state-of-the-art/binocular/design/prototype_1/kicad/prototype_testboard-1/03_Connector.kicad_sch

## KiCad design design/prototype_1/kicad/prototype_testboard-1/03_Connector.kicad_sch (2022-01-14)

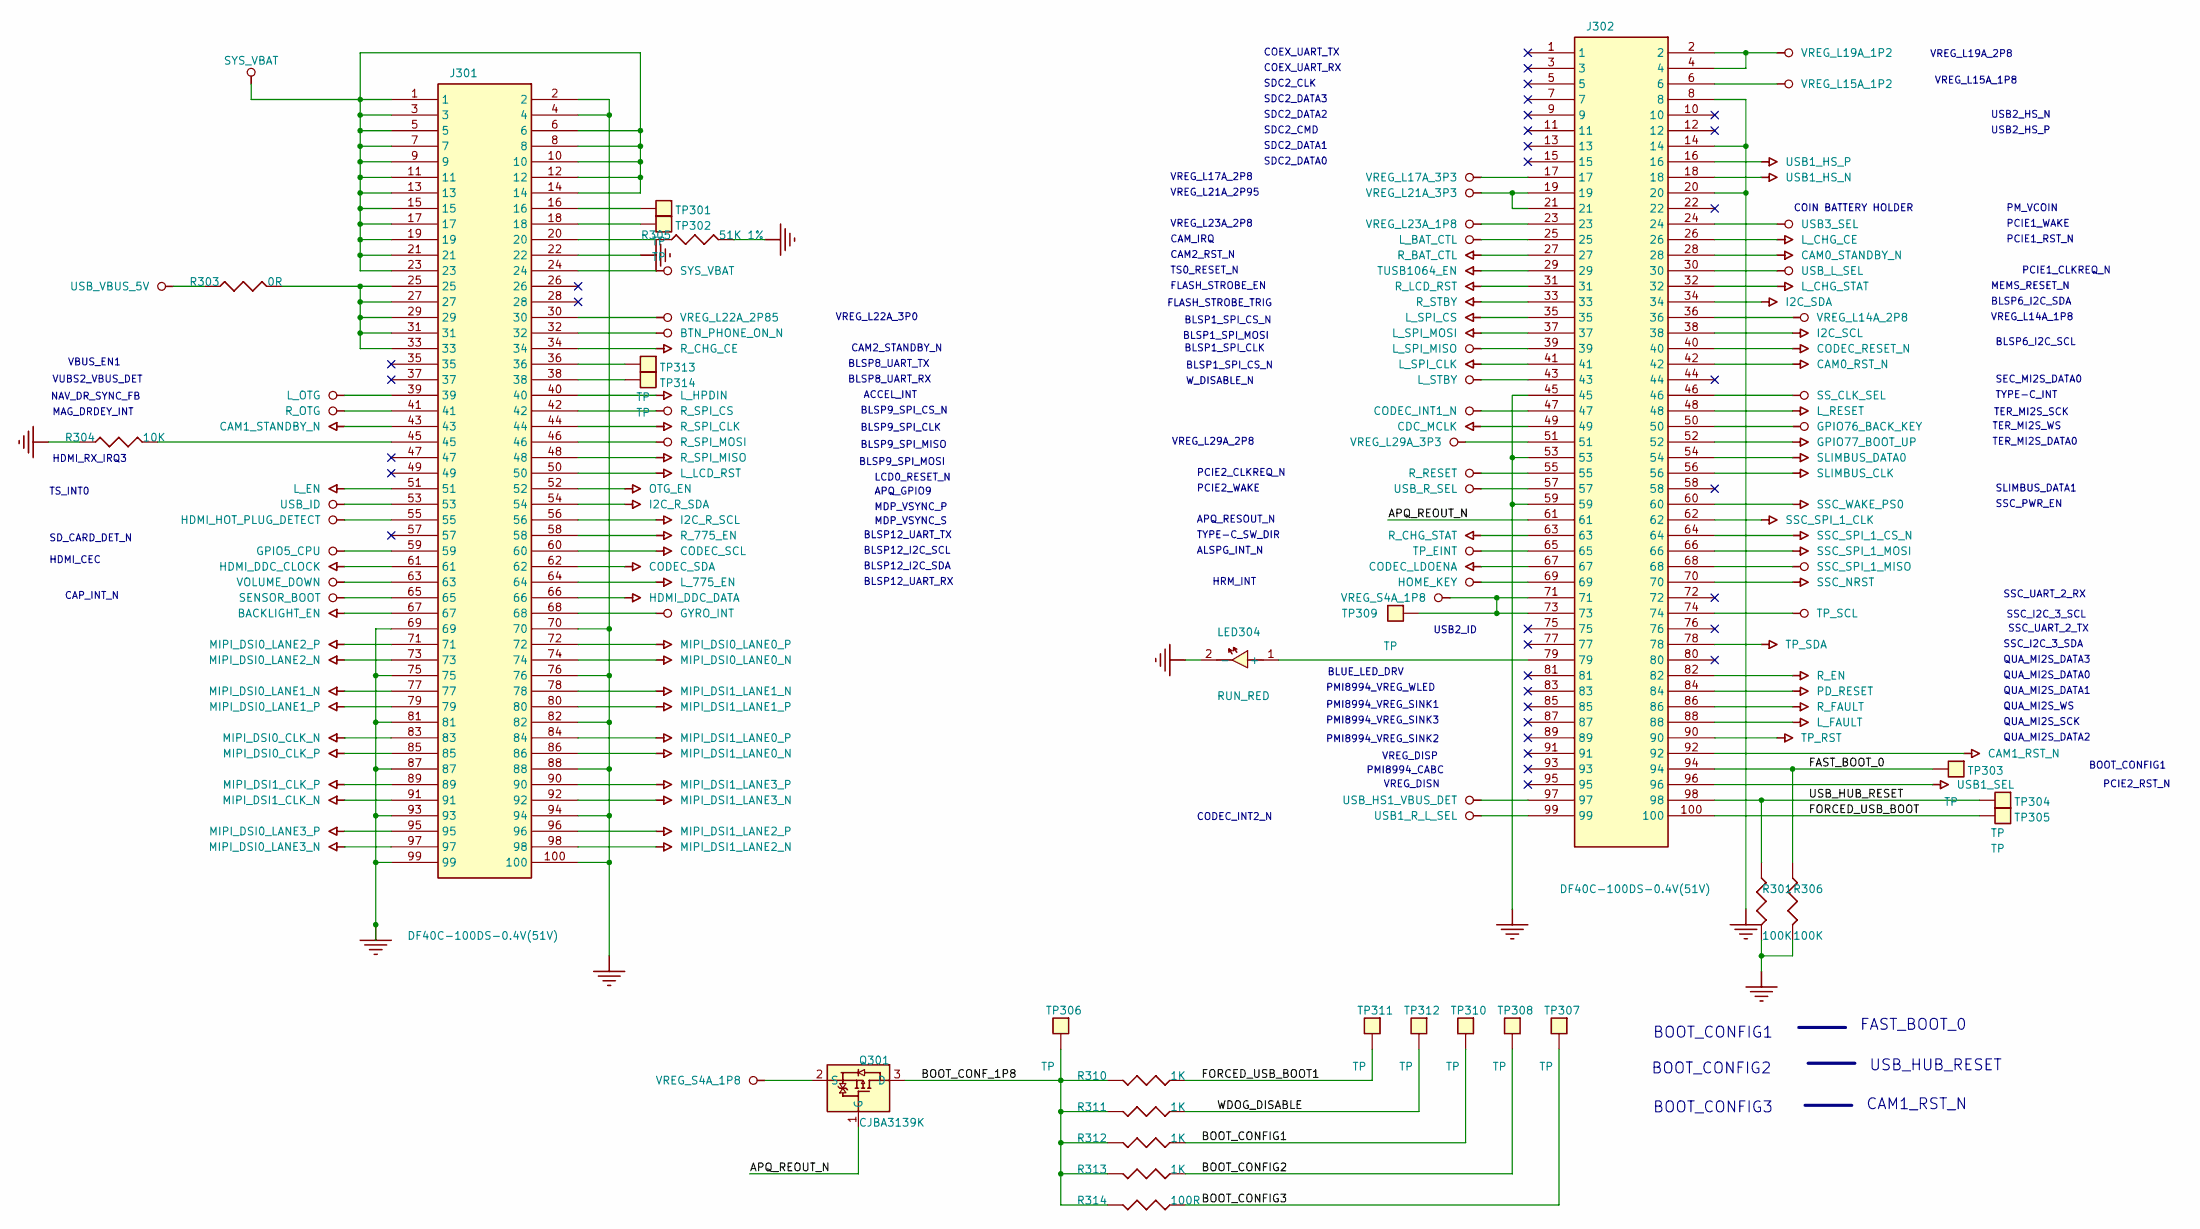
[picture p25: schematic 03_Connector.kicad_sch]

Parts:
J301, J302: DF40C-100DS-0.4V(51V); DF40C-100DS
LED304: RUN_RED; LED_0603
Q301: CJBA3139K; DFN1006-3L
R301, R306: 100K; R0201
R303: 0R; R0805
R304: 10K; R0201
R305: 51K 1%; R0201
R310, R311, R312, R313: 1K; R0201
R314: 100R; R0201
TP301, TP302, TP303, TP304, TP305, TP306, TP307, TP308, TP309, TP310, TP311, TP312, TP313, TP314: TP; TP-D1r0

Connections:
APQ_REOUT_N: J302.61, Q301.1 (G)
BOOT_CONFIG1: R312.1, TP310.1
BOOT_CONFIG2: R313.1, TP308.1
BOOT_CONFIG3: R314.1, TP307.1
BOOT_CONF_1P8: Q301.3 (D), R310.2, R311.2, R312.2, R313.2, R314.2, TP306.1
FAST_BOOT_0: J302.94, R306.1, TP303.1
FORCED_USB_BOOT: J302.100, TP305.1
FORCED_USB_BOOT1: R310.1, TP311.1
unnamed: J301.1, J301.3, J301.5, J301.6, J301.7, J301.8, J301.9, J301.10, J301.11, J301.12, J301.13, J301.14, J301.15, J301.17, J301.19, J301.21, J301.23
unnamed: J301.16, TP301.1
unnamed: J301.18, TP302.1
unnamed: J301.20, R305.1
unnamed: J301.25, J301.27, J301.29, J301.31, J301.33, R303.2
unnamed: J301.36, TP313.1
unnamed: J301.38, TP314.1
unnamed: J301.45, R304.2
unnamed: J301.69, J301.75, J301.81, J301.87, J301.93, J301.99
unnamed: J301.2, J301.4, J301.70, J301.76, J301.82, J301.88, J301.94, J301.100
unnamed: J302.2, J302.4
unnamed: J302.8, J302.14, J302.20
unnamed: J302.19, J302.21
unnamed: J302.45, J302.53, J302.59
unnamed: J302.71, J302.73, TP309.1
unnamed: J302.79, LED304.1 (+)
unnamed: R301.2, R306.2
USB_HUB_RESET: J302.98, R301.1, TP304.1
WDOG_DISABLE: R311.1, TP312.1

Notes on the sheet:
APQ_GPIO9
HDMI_CEC
BLSP12_I2C_SCL
VUBS2_VBUS_DET
BLSP1_SPI_CLK
BLSP9_SPI_CLK
QUA_MI2S_DATA3
SDC2_CLK
BLSP1_SPI_CS_N
VREG_DISP
MDP_VSYNC_P
QUA_MI2S_DATA1
BLUE_LED_DRV
USB2_HS_N
COEX_UART_RX
CAM2_STANDBY_N
PCIE2_RST_N
TS_INT0
SSC_UART_2_TX
MAG_DRDEY_INT
BOOT_CONFIG1
CAM2_RST_N
PMI8994_CABC
FLASH_STROBE_TRIG
BLSP12_UART_RX
VREG_L29A_2P8
PMI8994_VREG_SINK1
TS0_RESET_N
ALSPG_INT_N
COEX_UART_TX
MEMS_RESET_N
QUA_MI2S_WS
CODEC_INT2_N
CAM1_RST_N
VBUS_EN1
SD_CARD_DET_N
BLSP8_UART_RX
QUA_MI2S_SCK
PCIE1_WAKE
VREG_DISN
PCIE1_RST_N
USB2_ID
PM_VCOIN
SSC_UART_2_RX
SSC_I2C_3_SCL
USB2_HS_P
SEC_MI2S_DATA0
COIN BATTERY HOLDER
VREG_L23A_2P8
VREG_L17A_2P8
QUA_MI2S_DATA0
MDP_VSYNC_S
BLSP1_SPI_MOSI
PCIE1_CLKREQ_N
SDC2_DATA3
TYPE-C_SW_DIR
VREG_L21A_2P95
PMI8994_VREG_SINK3
VREG_L19A_2P8
SDC2_DATA0
BOOT_CONFIG2
PMI8994_VREG_WLED
HRM_INT
BLSP9_SPI_MISO
TER_MI2S_WS
BLSP6_I2C_SDA
BOOT_CONFIG3
BLSP8_UART_TX
LCD0_RESET_N
FLASH_STROBE_EN
SSC_I2C_3_SDA
PCIE2_CLKREQ_N
TER_MI2S_DATA0
BLSP12_UART_TX
PCIE2_WAKE
W_DISABLE_N
VREG_L15A_1P8
SDC2_DATA1
ACCEL_INT
NAV_DR_SYNC_FB
CAP_INT_N
BLSP6_I2C_SCL
BLSP12_I2C_SDA
FAST_BOOT_0
PMI8994_VREG_SINK2
SDC2_DATA2
HDMI_RX_IRQ3
TYPE-C_INT
TER_MI2S_SCK
CAM_IRQ
SDC2_CMD
APQ_RESOUT_N
VREG_L22A_3P0
SSC_PWR_EN
VREG_L14A_1P8
BLSP9_SPI_MOSI
SLIMBUS_DATA1
BLSP9_SPI_CS_N
QUA_MI2S_DATA2
USB_HUB_RESET
