state-of-the-art/binocular/design/prototype_1/kicad/prototype_testboard-1/04_TUSB564.kicad_sch

## KiCad design design/prototype_1/kicad/prototype_testboard-1/04_TUSB564.kicad_sch (2022-01-14)

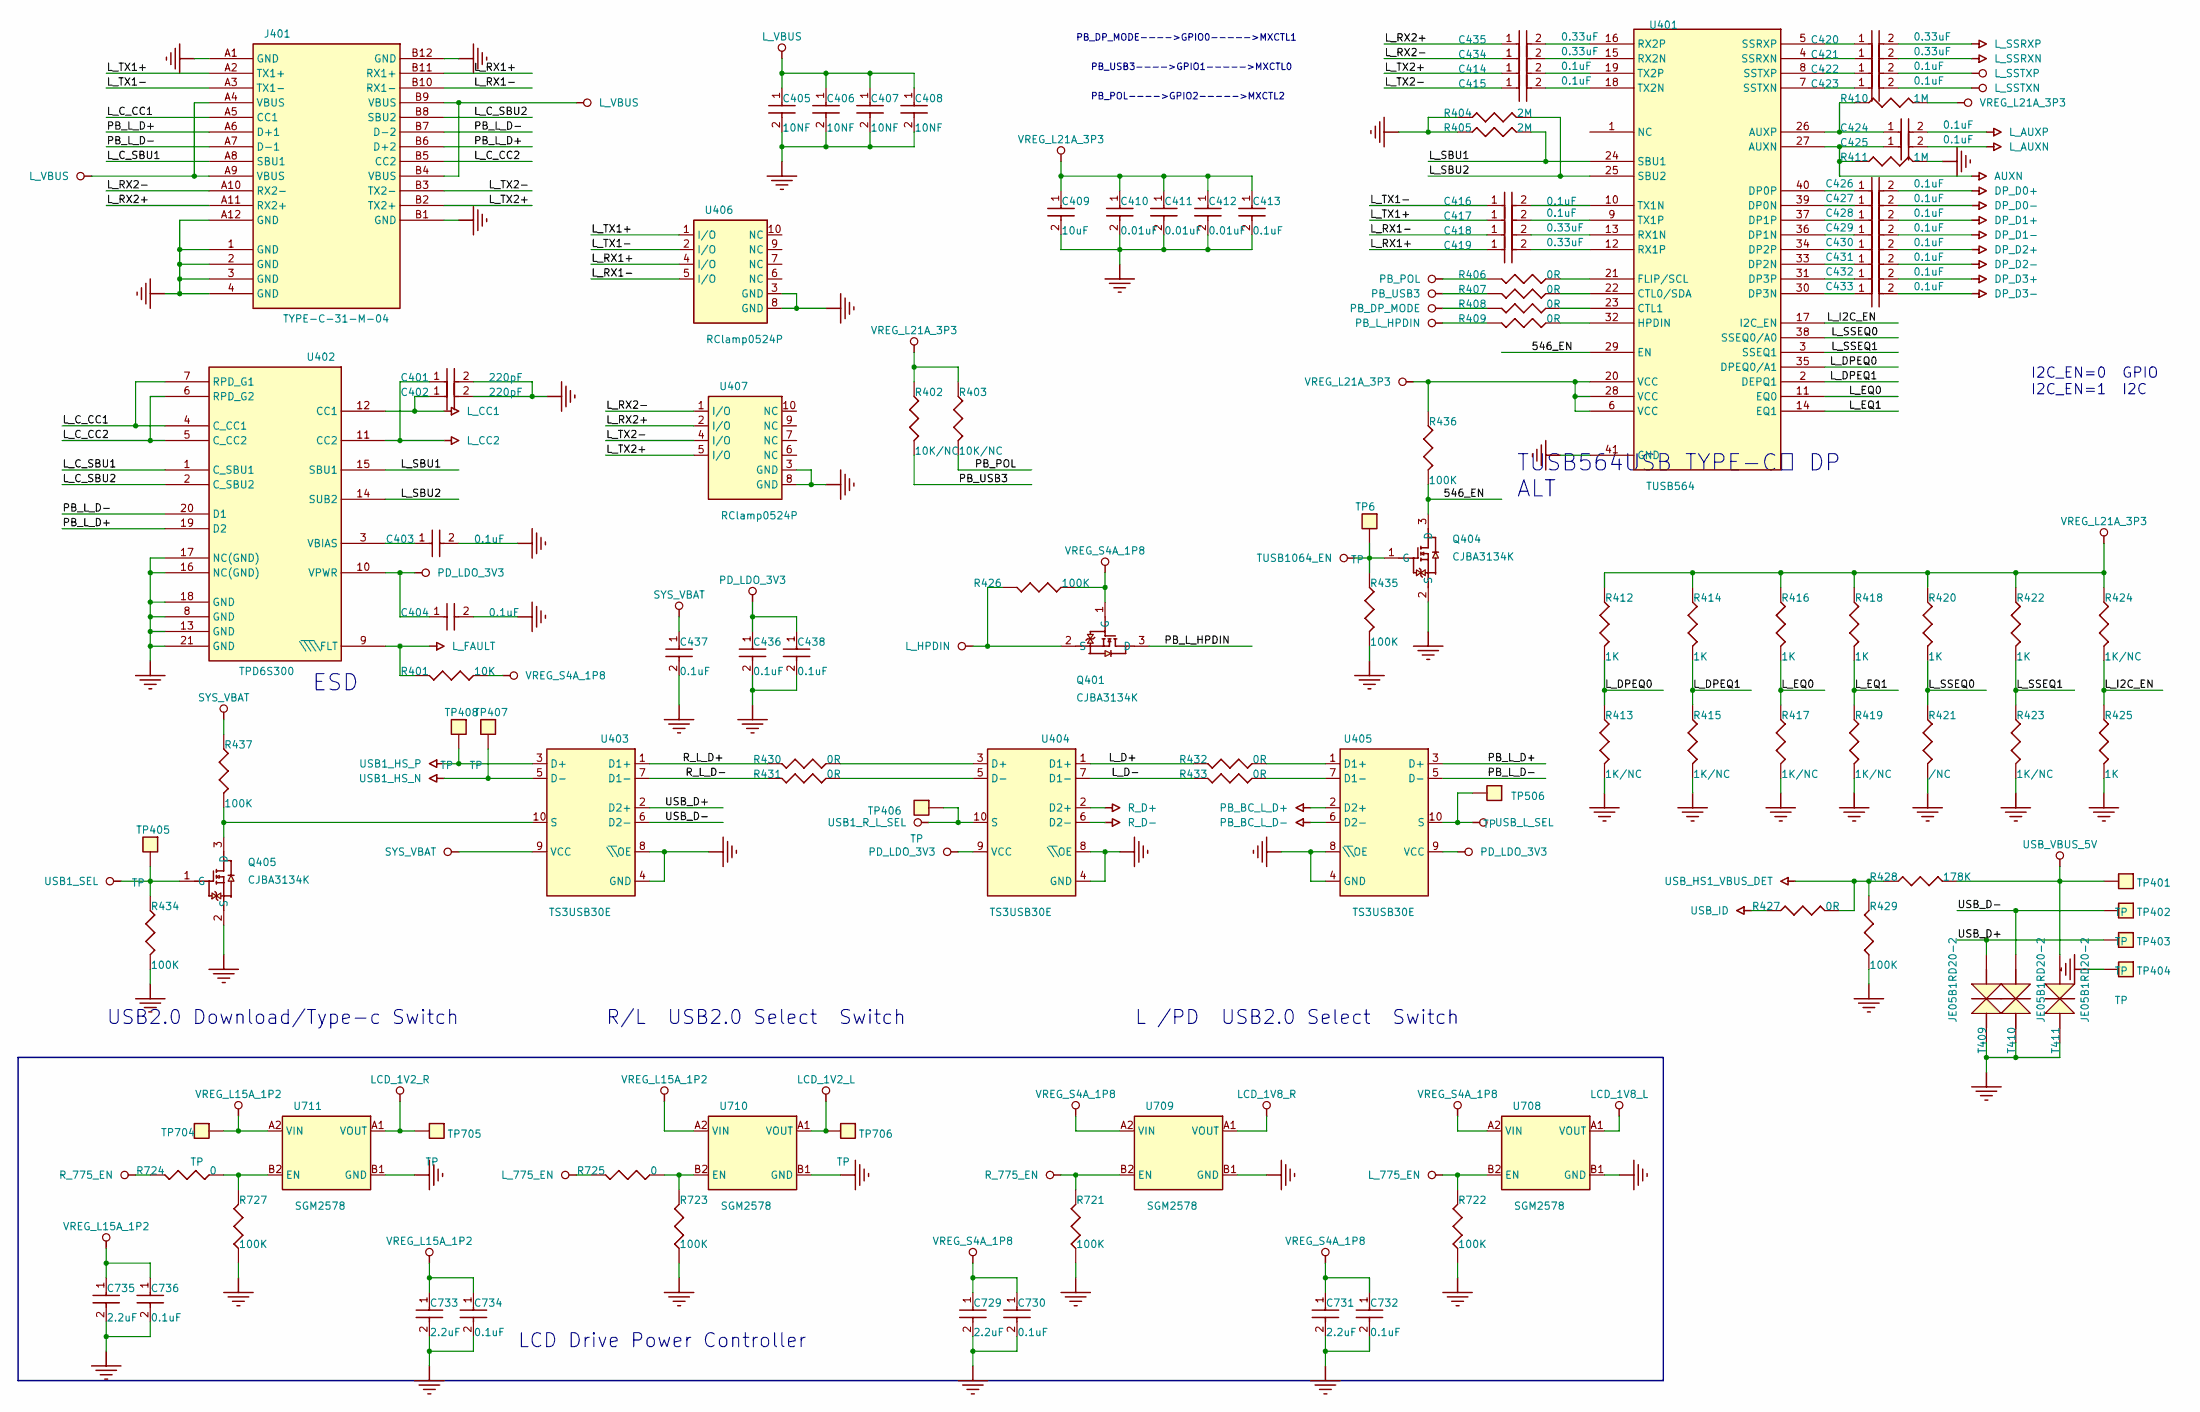
[picture p26: schematic 04_TUSB564.kicad_sch]

Parts:
C401, C402: 220pF; C0201
C403, C404, C413, C414, C415, C416, C417, C422, C423, C424, C425, C426, C427, C428, C429, C430, C431, C432, C433, C436, C437, C438, C730, C732, C734, C736: 0.1uF; C0201
C405, C406, C407, C408: 10NF; C0201
C409: 10uF; C0201
C410, C411, C412: 0.01uF; C0201
C418, C419, C420, C421, C434, C435: 0.33uF; C0201
C729, C731, C733, C735: 2.2uF; C0201
J401: TYPE-C-31-M-04
Q401, Q404, Q405: CJBA3134K; DFN1006-3L
R401: 10K; R0201
R402, R403: 10K/NC; R0201
R404, R405: 2M; R0201
R406, R407, R408, R409, R427, R430, R431, R432, R433: 0R; R0201
R410, R411: 1M; R0201
R412, R414, R416, R418, R420, R422, R425: 1K; R0201
R413, R415, R417, R419, R423, R424: 1K/NC; R0201
R421: /NC; R0201
R426, R429, R434, R435, R436, R437, R721, R722, R723, R727: 100K; R0201
R428: 178K; R0201
R724, R725: 0; R0201
T409, T410, T411: JE05B1RD20-2; DFN1006-2; MANUFACTURER PART NUMBER RB551V-30TE-17
TP6, TP401, TP402, TP403, TP404, TP405, TP406, TP407, TP408, TP506, TP704, TP705, TP706: TP; TP-D1r0
U401: TUSB564; TUSB564_WQFN40
U402: TPD6S300; TPD6S300_WQFN
U403, U404, U405: TS3USB30E; TS3USB30E_UQFN
U406, U407: RClamp0524P
U708, U709, U710, U711: SGM2578; WLCSP-0r90r9-4B

Connections:
546_EN: Q404.3 (D), R436.2, U401.29 (EN)
L_C_CC1: J401.A5 (CC1), U402.4 (C_CC1), U402.7 (RPD_G1)
L_C_CC2: J401.B5 (CC2), U402.5 (C_CC2), U402.6 (RPD_G2)
L_C_SBU1: J401.A8 (SBU1), U402.1 (C_SBU1)
L_C_SBU2: J401.B8 (SBU2), U402.2 (C_SBU2)
L_D+: R432.2, U404.1 (D1+)
L_D-: R433.2, U404.7 (D1-)
L_DPEQ0: R412.2, R413.1, U401.35 (DPEQ0/A1)
L_DPEQ1: R414.2, R415.1, U401.2 (DEPQ1)
L_EQ0: R416.2, R417.1, U401.11 (EQ0)
L_EQ1: R418.2, R419.1, U401.14 (EQ1)
L_I2C_EN: R424.2, R425.1, U401.17 (I2C_EN)
L_RX1+: C419.1, J401.B11 (RX1+), U406.4 (I/O)
L_RX1-: C418.1, J401.B10 (RX1-), U406.5 (I/O)
L_RX2+: C435.1, J401.A11 (RX2+), U407.2 (I/O)
L_RX2-: C434.1, J401.A10 (RX2-), U407.1 (I/O)
L_SBU1: R405.2, U401.24 (SBU1), U402.15 (SBU1)
L_SBU2: R404.2, U401.25 (SBU2), U402.14 (SUB2)
L_SSEQ0: R420.2, R421.1, U401.38 (SSEQ0/A0)
L_SSEQ1: R422.2, R423.1, U401.3 (SSEQ1)
L_TX1+: C417.1, J401.A2 (TX1+), U406.1 (I/O)
L_TX1-: C416.1, J401.A3 (TX1-), U406.2 (I/O)
L_TX2+: C414.1, J401.B2 (TX2+), U407.5 (I/O)
L_TX2-: C415.1, J401.B3 (TX2-), U407.4 (I/O)
unnamed: C401.1, U402.11 (CC2)
unnamed: C401.2, C402.2
unnamed: C402.1, U402.12 (CC1)
unnamed: C403.1, U402.3 (VBIAS)
unnamed: C404.1, U402.10 (VPWR)
unnamed: C405.1, C406.1, C407.1, C408.1
unnamed: C405.2, C406.2, C407.2, C408.2
unnamed: C409.1, C410.1, C411.1, C412.1, C413.1
unnamed: C409.2, C410.2, C411.2, C412.2, C413.2
unnamed: C414.2, U401.19 (TX2P)
unnamed: C415.2, U401.18 (TX2N)
unnamed: C416.2, U401.10 (TX1N)
unnamed: C417.2, U401.9 (TX1P)
unnamed: C418.2, U401.13 (RX1N)
unnamed: C419.2, U401.12 (RX1P)
unnamed: C420.1, U401.5 (SSRXP)
unnamed: C421.1, U401.4 (SSRXN)
unnamed: C422.1, U401.8 (SSTXP)
unnamed: C423.1, U401.7 (SSTXN)
unnamed: C424.1, R410.1, U401.26 (AUXP)
unnamed: C425.1, R411.1, U401.27 (AUXN)
unnamed: C426.1, U401.40 (DP0P)
unnamed: C427.1, U401.39 (DP0N)
unnamed: C428.1, U401.37 (DP1P)
unnamed: C429.1, U401.36 (DP1N)
unnamed: C430.1, U401.34 (DP2P)
unnamed: C431.1, U401.33 (DP2N)
unnamed: C432.1, U401.31 (DP3P)
unnamed: C433.1, U401.30 (DP3N)
unnamed: C434.2, U401.15 (RX2N)
unnamed: C435.2, U401.16 (RX2P)
unnamed: C436.1, C438.1
unnamed: C436.2, C438.2
unnamed: C729.1, C730.1
unnamed: C729.2, C730.2
unnamed: C731.1, C732.1
unnamed: C731.2, C732.2
unnamed: C733.1, C734.1
unnamed: C733.2, C734.2
unnamed: C735.1, C736.1
unnamed: C735.2, C736.2
unnamed: J401.1 (GND), J401.2 (GND), J401.3 (GND), J401.4 (GND), J401.A12 (GND)
unnamed: J401.A4 (VBUS), J401.A9 (VBUS)
unnamed: J401.B4 (VBUS), J401.B9 (VBUS)
unnamed: Q401.1 (G), R426.1
unnamed: Q401.2 (S), R426.2
unnamed: Q404.1 (G), R435.1, TP6.1
unnamed: Q405.1 (G), R434.1, TP405.1
unnamed: Q405.3 (D), R437.2, U403.10 (S)
unnamed: R401.2, U402.9 (~\\\\FLT)
unnamed: R402.1, R403.1
unnamed: R404.1, R405.1
unnamed: R406.1, U401.21 (FLIP/SCL)
unnamed: R407.1, U401.22 (CTL0/SDA)
unnamed: R408.1, U401.23 (CTL1)
unnamed: R409.1, U401.32 (HPDIN)
unnamed: R412.1, R414.1, R416.1, R418.1, R420.1, R422.1, R424.1
unnamed: R427.2, R428.1, R429.2
unnamed: R428.2, T411.2 (-), TP401.1
unnamed: R430.1, U404.3 (D+)
unnamed: R431.1, U404.5 (D-)
unnamed: R432.1, U405.1 (D1+)
unnamed: R433.1, U405.7 (D1-)
unnamed: R436.1, U401.6 (VCC), U401.20 (VCC), U401.28 (VCC)
unnamed: R721.2, U709.B2 (EN)
unnamed: R722.2, U708.B2 (EN)
unnamed: R723.2, R725.1, U710.B2 (EN)
unnamed: R724.1, R727.2, U711.B2 (EN)
unnamed: T409.1 (+), T410.1 (+), T411.1 (+)
unnamed: TP406.1, U404.10 (S)
unnamed: TP407.1, U403.5 (D-)
unnamed: TP408.1, U403.3 (D+)
unnamed: TP506.1, U405.10 (S)
unnamed: TP704.1, U711.A2 (VIN)
unnamed: TP705.1, U711.A1 (VOUT)
unnamed: TP706.1, U710.A1 (VOUT)
unnamed: U402.8 (GND), U402.13 (GND), U402.16 (NC(GND)), U402.17 (NC(GND)), U402.18 (GND), U402.21 (GND)
unnamed: U403.4 (GND), U403.8 (~\\OE)
unnamed: U404.4 (GND), U404.8 (~\\OE)
unnamed: U405.4 (GND), U405.8 (~\\OE)
unnamed: U406.3 (GND), U406.8 (GND)
unnamed: U407.3 (GND), U407.8 (GND)
PB_L_D+: J401.A6 (D+1), J401.B6 (D+2), U402.19 (D2), U405.3 (D+)
PB_L_D-: J401.A7 (D-1), J401.B7 (D-2), U402.20 (D1), U405.5 (D-)
PB_L_HPDIN: Q401.3 (D)
PB_POL: R403.2
PB_USB3: R402.2
R_L_D+: R430.2, U403.1 (D1+)
R_L_D-: R431.2, U403.7 (D1-)
USB_D+: T409.2 (-), TP403.1, U403.2 (D2+)
USB_D-: T410.2 (-), TP402.1, U403.6 (D2-)

Notes on the sheet:
LCD Drive Power Controller
TUSB564USB TYPE-C™ DP ALT
R/L USB2.0 Select Switch
PB_DP_MODE---->GPIO0----->MXCTL1
L /PD USB2.0 Select Switch
PB_POL---->GPIO2----->MXCTL2
USB2.0 Download/Type-c Switch
ESD
I2C_EN=0 GPIO I2C_EN=1 I2C
PB_USB3---->GPIO1----->MXCTL0
