state-of-the-art/binocular/design/prototype_1/kicad/prototype_testboard-1/05_TUSB546-DSI.kicad_sch

## KiCad design design/prototype_1/kicad/prototype_testboard-1/05_TUSB546-DSI.kicad_sch (2022-01-14)

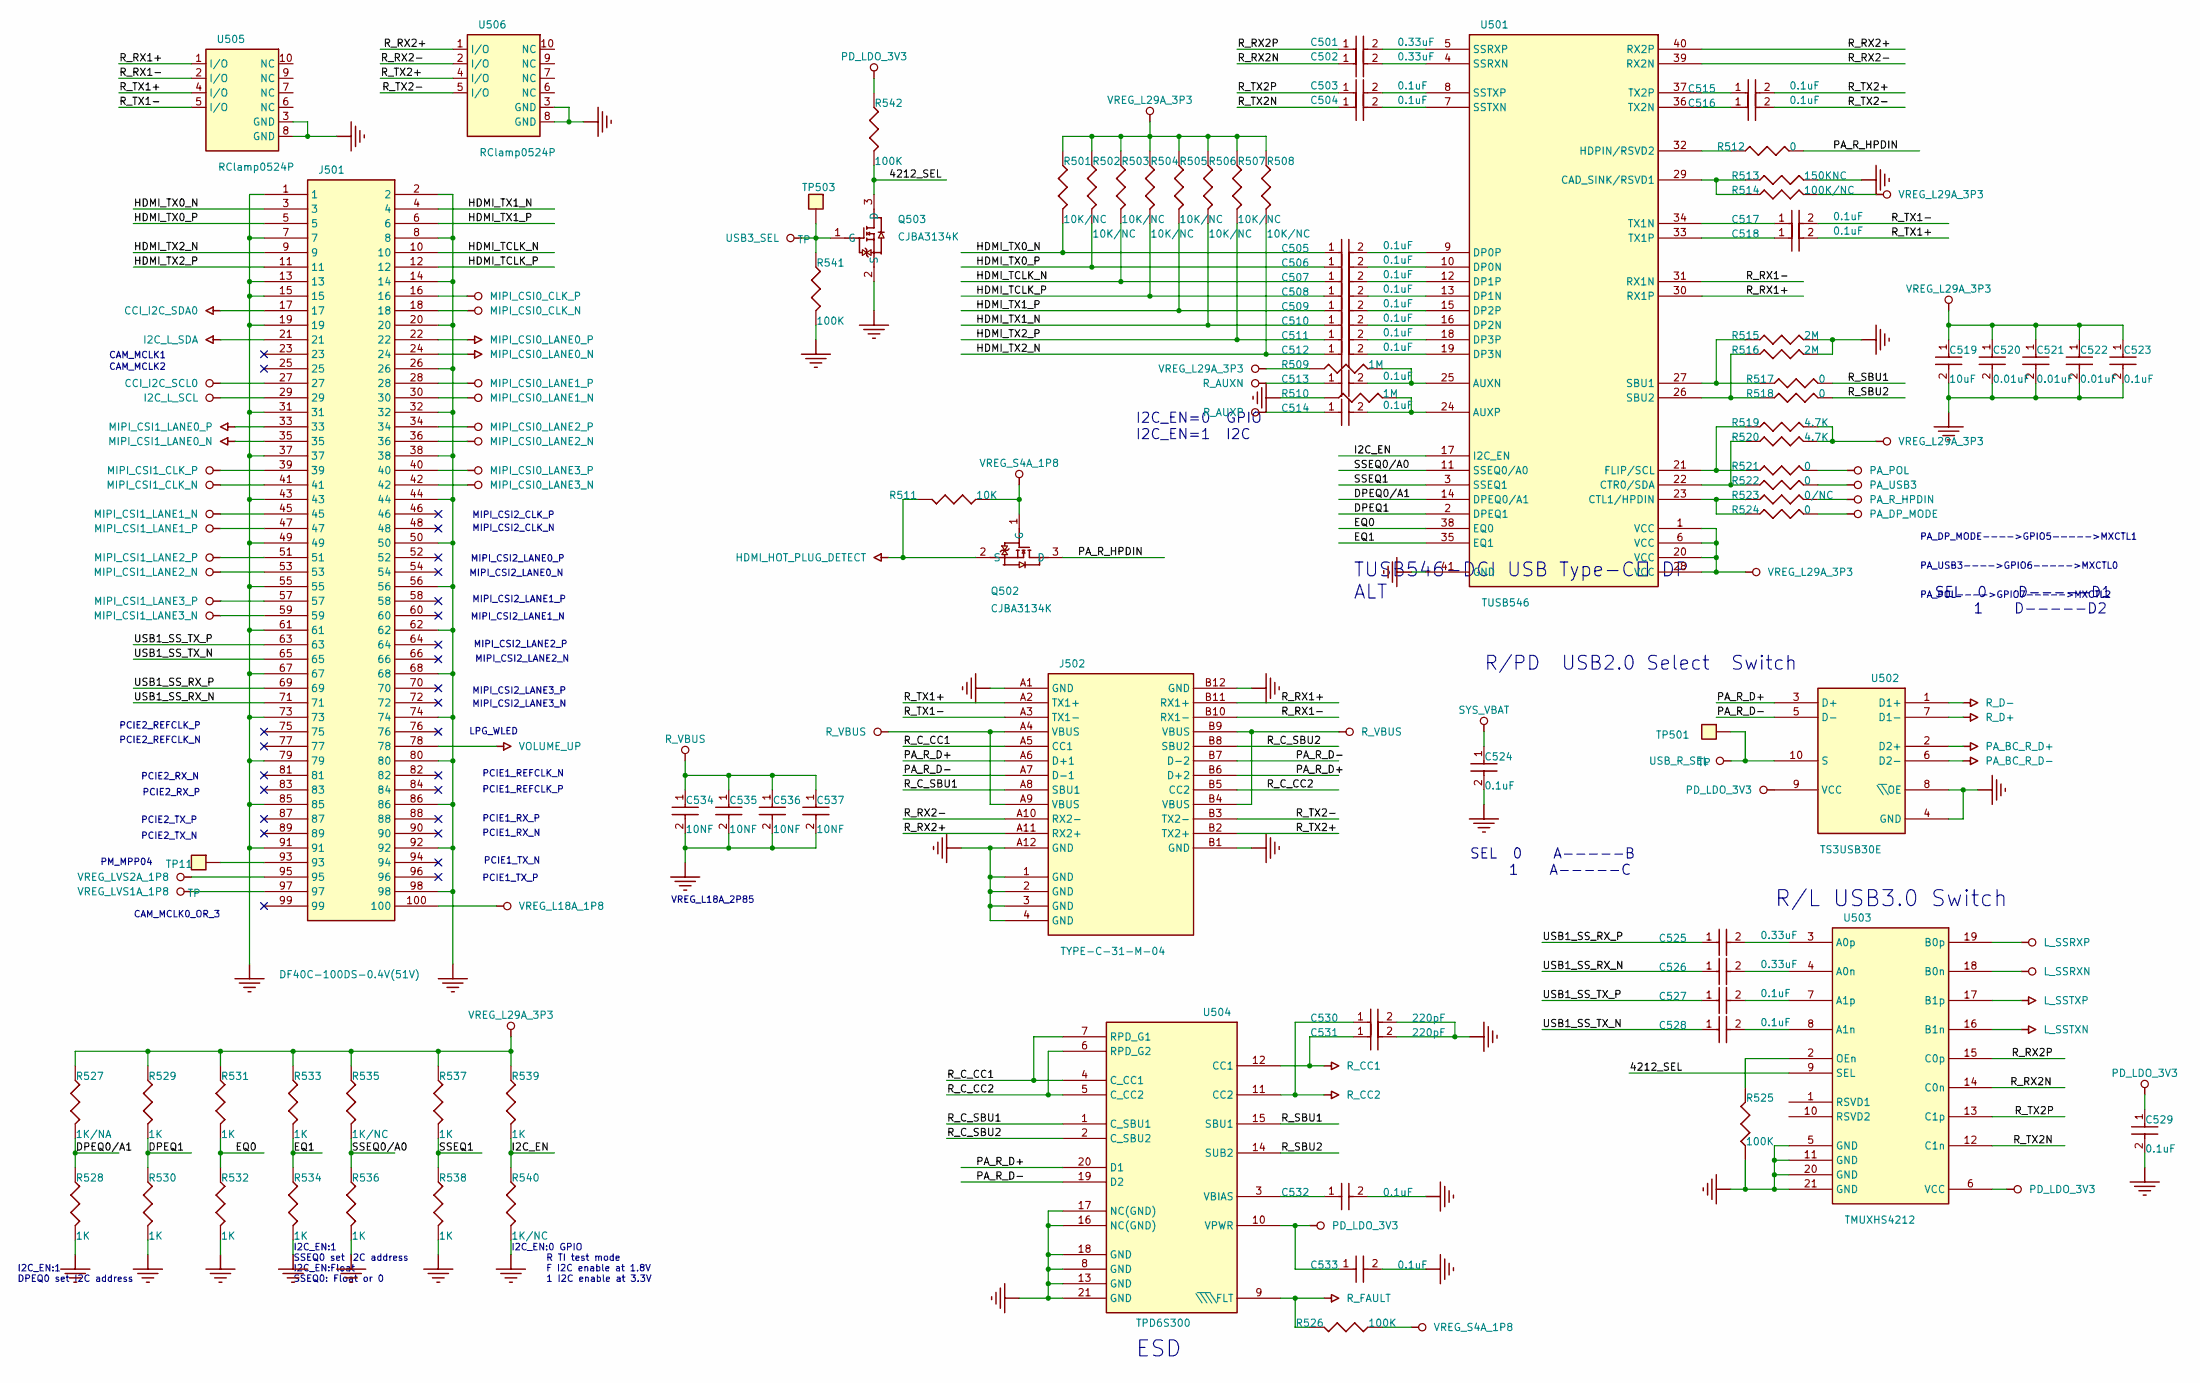
[picture p27: schematic 05_TUSB546-DSI.kicad_sch]

Parts:
C501, C502, C525, C526: 0.33uF; C0201
C503, C504, C505, C506, C507, C508, C509, C510, C511, C512, C513, C514, C515, C516, C517, C518, C523, C524, C527, C528, C529, C532, C533: 0.1uF; C0201
C519: 10uF; C0201
C520, C521, C522: 0.01uF; C0201
C530, C531: 220pF; C0201
C534, C535, C536, C537: 10NF; C0201
J501: DF40C-100DS-0.4V(51V); DF40C-100DS
J502: TYPE-C-31-M-04
Q502, Q503: CJBA3134K; DFN1006-3L
R501, R502, R503, R504, R505, R506, R507, R508: 10K/NC; R0201
R509, R510: 1M; R0201
R511: 10K; R0201
R512, R517, R518, R521, R522, R524: 0; R0201
R513: 150KNC; R0201
R514: 100K/NC; R0201
R515, R516: 2M; R0201
R519, R520: 4.7K; R0201
R523: 0/NC; R0201
R525, R526, R541, R542: 100K; R0201
R527: 1K/NA; R0201
R528, R529, R530, R531, R532, R533, R534, R536, R537, R538, R539: 1K; R0201
R535, R540: 1K/NC; R0201
TP11, TP501, TP503: TP; TP-D1r0
U501: TUSB546; TUSB564_WQFN40
U502: TS3USB30E; TS3USB30E_UQFN
U503: TMUXHS4212; TMUXHS4212_VQFN
U504: TPD6S300; TPD6S300_WQFN
U505, U506: RClamp0524P

Connections:
4212_SEL: Q503.3 (D), R542.2, U503.9 (SEL)
DPEQ0/A1: R527.2, R528.1, U501.14 (DPEQ0/A1)
DPEQ1: R529.2, R530.1, U501.2 (DPEQ1)
EQ0: R531.2, R532.1, U501.38 (EQ0)
EQ1: R533.2, R534.1, U501.35 (EQ1)
HDMI_TCLK_N: C507.1, J501.10, R503.2
HDMI_TCLK_P: C508.1, J501.12, R504.2
HDMI_TX0_N: C505.1, J501.3, R501.2
HDMI_TX0_P: C506.1, J501.5, R502.2
HDMI_TX1_N: C510.1, J501.4, R506.2
HDMI_TX1_P: C509.1, J501.6, R505.2
HDMI_TX2_N: C512.1, J501.9, R508.2
HDMI_TX2_P: C511.1, J501.11, R507.2
I2C_EN: R539.2, R540.1, U501.17 (I2C_EN)
unnamed: C501.2, U501.5 (SSRXP)
unnamed: C502.2, U501.4 (SSRXN)
unnamed: C503.2, U501.8 (SSTXP)
unnamed: C504.2, U501.7 (SSTXN)
unnamed: C505.2, U501.9 (DP0P)
unnamed: C506.2, U501.10 (DP0N)
unnamed: C507.2, U501.12 (DP1P)
unnamed: C508.2, U501.13 (DP1N)
unnamed: C509.2, U501.15 (DP2P)
unnamed: C510.2, U501.16 (DP2N)
unnamed: C511.2, U501.18 (DP3P)
unnamed: C512.2, U501.19 (DP3N)
unnamed: C513.2, R509.2, U501.25 (AUXN)
unnamed: C514.2, R510.2, U501.24 (AUXP)
unnamed: C515.1, U501.37 (TX2P)
unnamed: C516.1, U501.36 (TX2N)
unnamed: C517.1, U501.34 (TX1N)
unnamed: C518.1, U501.33 (TX1P)
unnamed: C519.1, C520.1, C521.1, C522.1, C523.1
unnamed: C519.2, C520.2, C521.2, C522.2, C523.2
unnamed: C525.2, U503.3 (A0p)
unnamed: C526.2, U503.4 (A0n)
unnamed: C527.2, U503.7 (A1p)
unnamed: C528.2, U503.8 (A1n)
unnamed: C530.1, U504.11 (CC2)
unnamed: C530.2, C531.2
unnamed: C531.1, U504.12 (CC1)
unnamed: C532.1, U504.3 (VBIAS)
unnamed: C533.1, U504.10 (VPWR)
unnamed: C534.1, C535.1, C536.1, C537.1
unnamed: C534.2, C535.2, C536.2, C537.2
unnamed: J501.1, J501.7, J501.13, J501.15, J501.19, J501.31, J501.37, J501.43, J501.49, J501.55, J501.61, J501.67, J501.73, J501.79, J501.85, J501.91
unnamed: J501.2, J501.8, J501.14, J501.20, J501.26, J501.32, J501.38, J501.44, J501.50, J501.56, J501.62, J501.68, J501.74, J501.80, J501.86, J501.92, J501.98
unnamed: J501.93, TP11.1
unnamed: J502.1 (GND), J502.2 (GND), J502.3 (GND), J502.4 (GND), J502.A12 (GND)
unnamed: J502.A4 (VBUS), J502.A9 (VBUS)
unnamed: J502.B4 (VBUS), J502.B9 (VBUS)
unnamed: Q502.1 (G), R511.1
unnamed: Q502.2 (S), R511.2
unnamed: Q503.1 (G), R541.1, TP503.1
unnamed: R501.1, R502.1, R503.1, R504.1, R505.1, R506.1, R507.1, R508.1
unnamed: R512.1, U501.32 (HDPIN/RSVD2)
unnamed: R513.1, R514.1, U501.29 (CAD_SINK/RSVD1)
unnamed: R515.1, R517.1, U501.27 (SBU1)
unnamed: R515.2, R516.2
unnamed: R516.1, R518.1, U501.26 (SBU2)
unnamed: R519.1, R521.1, U501.21 (FLIP/SCL)
unnamed: R519.2, R520.2
unnamed: R520.1, R522.1, U501.22 (CTR0/SDA)
unnamed: R523.1, R524.1, U501.23 (CTL1/HPDIN)
unnamed: R525.1, U503.5 (GND), U503.11 (GND), U503.20 (GND), U503.21 (GND)
unnamed: R525.2, U503.2 (OEn)
unnamed: R526.2, U504.9 (~\\\\FLT)
unnamed: R527.1, R529.1, R531.1, R533.1, R535.1, R537.1, R539.1
unnamed: TP501.1, U502.10 (S)
unnamed: U501.1 (VCC), U501.6 (VCC), U501.20 (VCC), U501.28 (VCC)
unnamed: U502.4 (GND), U502.8 (~\\OE)
unnamed: U504.8 (GND), U504.13 (GND), U504.16 (NC(GND)), U504.17 (NC(GND)), U504.18 (GND), U504.21 (GND)
unnamed: U505.3 (GND), U505.8 (GND)
unnamed: U506.3 (GND), U506.8 (GND)
PA_R_D+: J502.A6 (D+1), J502.B6 (D+2), U502.3 (D+), U504.20 (D1)
PA_R_D-: J502.A7 (D-1), J502.B7 (D-2), U502.5 (D-), U504.19 (D2)
PA_R_HPDIN: Q502.3 (D), R512.2
R_C_CC1: J502.A5 (CC1), U504.4 (C_CC1), U504.7 (RPD_G1)
R_C_CC2: J502.B5 (CC2), U504.5 (C_CC2), U504.6 (RPD_G2)
R_C_SBU1: J502.A8 (SBU1), U504.1 (C_SBU1)
R_C_SBU2: J502.B8 (SBU2), U504.2 (C_SBU2)
R_RX1+: J502.B11 (RX1+), U501.30 (RX1P), U505.1 (I/O)
R_RX1-: J502.B10 (RX1-), U501.31 (RX1N), U505.2 (I/O)
R_RX2+: J502.A11 (RX2+), U501.40 (RX2P), U506.1 (I/O)
R_RX2-: J502.A10 (RX2-), U501.39 (RX2N), U506.2 (I/O)
R_RX2N: C502.1, U503.14 (C0n)
R_RX2P: C501.1, U503.15 (C0p)
R_SBU1: R517.2, U504.15 (SBU1)
R_SBU2: R518.2, U504.14 (SUB2)
R_TX1+: C518.2, J502.A2 (TX1+), U505.4 (I/O)
R_TX1-: C517.2, J502.A3 (TX1-), U505.5 (I/O)
R_TX2+: C515.2, J502.B2 (TX2+), U506.4 (I/O)
R_TX2-: C516.2, J502.B3 (TX2-), U506.5 (I/O)
R_TX2N: C504.1, U503.12 (C1n)
R_TX2P: C503.1, U503.13 (C1p)
SSEQ0/A0: R535.2, R536.1, U501.11 (SSEQ0/A0)
SSEQ1: R537.2, R538.1, U501.3 (SSEQ1)
USB1_SS_RX_N: C526.1, J501.71
USB1_SS_RX_P: C525.1, J501.69
USB1_SS_TX_N: C528.1, J501.65
USB1_SS_TX_P: C527.1, J501.63

Notes on the sheet:
PCIE1_REFCLK_P
PCIE1_RX_N
MIPI_CSI2_LANE1_N
PA_USB3---->GPIO6----->MXCTL0
PCIE2_RX_P
PCIE1_REFCLK_N
R/L USB3.0 Switch
MIPI_CSI2_CLK_N
R/PD USB2.0 Select Switch
PM_MPP04
I2C_EN:0 GPIO R TI test mode F I2C enable at 1.8V 1 I2C enable at 3.3V
VREG_L18A_2P85
MIPI_CSI2_LANE3_N
SEL 0 D-----D1 1 D-----D2
CAM_MCLK1
MIPI_CSI2_LANE2_N
TUSB546-DCI USB Type-C™ DP ALT
MIPI_CSI2_CLK_P
CAM_MCLK0_OR_3
MIPI_CSI2_LANE3_P
LPG_WLED
I2C_EN:1 SSEQ0 set I2C address I2C_EN:Float SSEQ0: Float or 0
PA_POL---->GPIO7----->MXCTL2
PCIE2_TX_P
I2C_EN=0 GPIO I2C_EN=1 I2C
SEL 0 A-----B 1 A-----C
PCIE1_RX_P
PCIE2_REFCLK_N
PCIE2_TX_N
PCIE2_RX_N
ESD
PCIE1_TX_P
PCIE1_TX_N
CAM_MCLK2
MIPI_CSI2_LANE2_P
MIPI_CSI2_LANE0_N
I2C_EN:1 DPEQ0 set I2C address
MIPI_CSI2_LANE0_P
PA_DP_MODE---->GPIO5----->MXCTL1
MIPI_CSI2_LANE1_P
PCIE2_REFCLK_P
