state-of-the-art/binocular/design/prototype_1/kicad/prototype_testboard-1/06_LCD_DRIVE.kicad_sch

## KiCad design design/prototype_1/kicad/prototype_testboard-1/06_LCD_DRIVE.kicad_sch (2022-01-14)

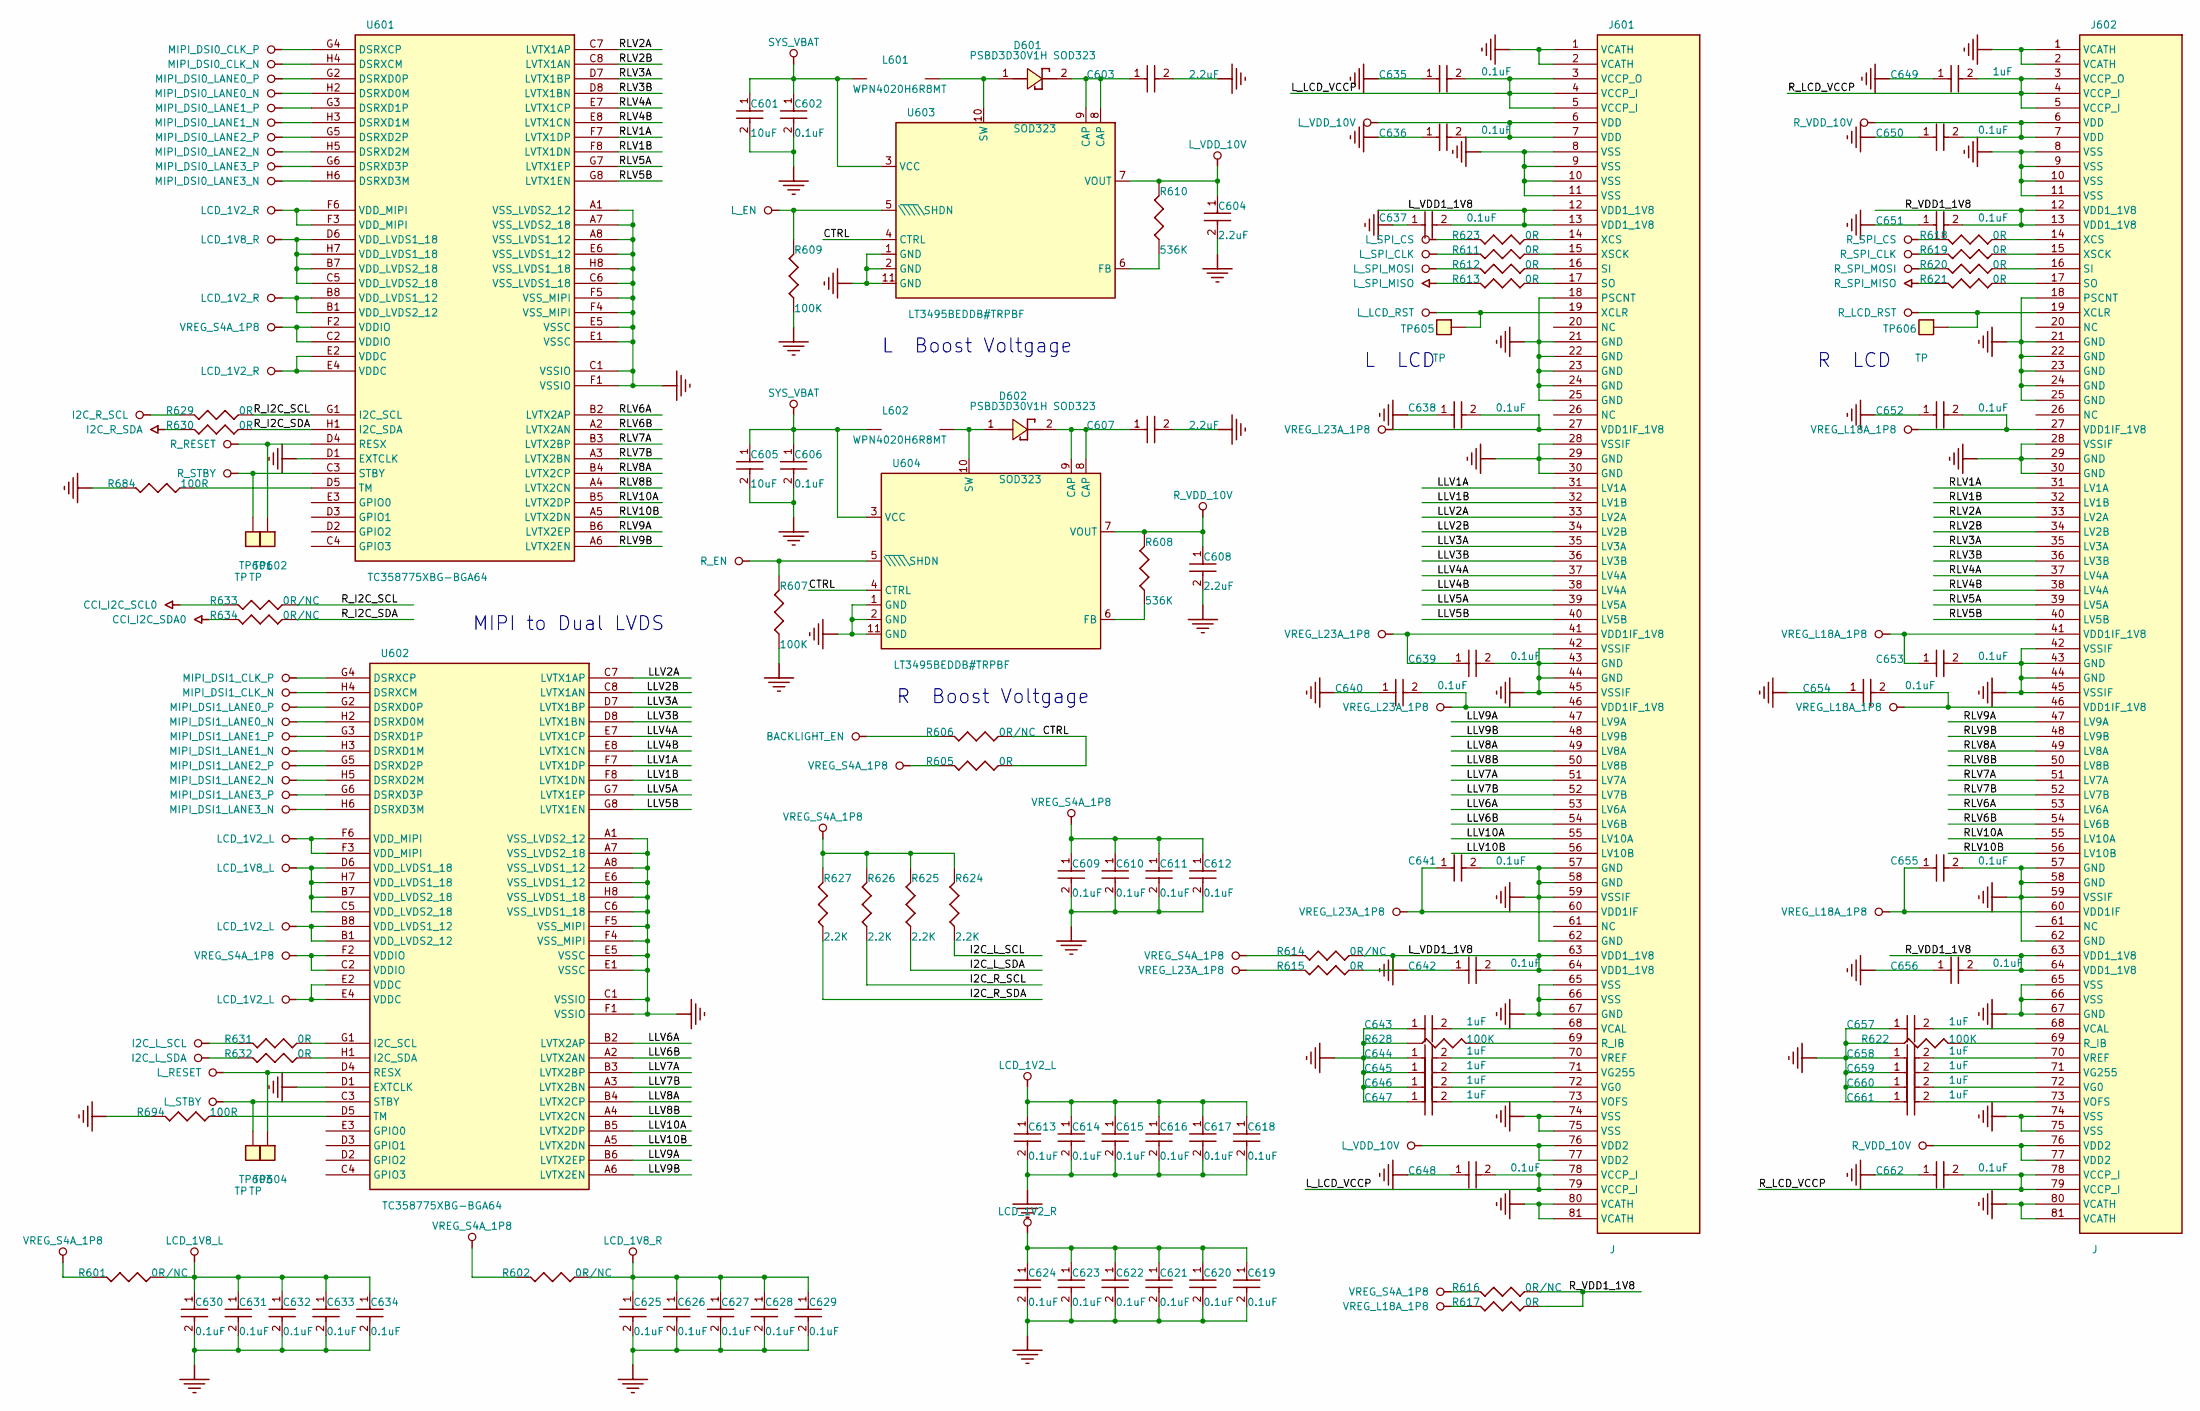
[picture p28: schematic 06_LCD_DRIVE.kicad_sch]

Parts:
C601, C605: 10uF; C0201
C602, C606, C609, C610, C611, C612, C613, C614, C615, C616, C617, C618, C619, C620, C621, C622, C623, C624, C625, C626, C627, C628, C629, C630, C631, C632, C633, C634, C635, C636, C637, C638, C639, C640, C641, C642, C648, C650, C651, C652, C653, C654, C655, C656, C662: 0.1uF; C0201
C603, C604, C607, C608: 2.2uF; C0201
C643, C644, C645, C646, C647, C649, C657, C658, C659, C660, C661: 1uF; C0201
D601, D602: PSBD3D30V1H SOD323; DIODE{slash}DIP{slash}P10.0
J601, J602: J; FF0881SA1-R3000
L601, L602: WPN4020H6R8MT; L{slash}IND{slash}SMD{slash}2520
R601, R602: 0R/NC; R0402
R605, R611, R612, R613, R615, R617, R618, R619, R620, R621, R623, R629, R630, R631, R632: 0R; R0201
R606, R614, R616, R633, R634: 0R/NC; R0201
R607, R609, R622, R628: 100K; R0201
R608, R610: 536K; R0201
R624, R625, R626, R627: 2.2K; R0201
R684, R694: 100R; R0201
TP601, TP602, TP603, TP604, TP605, TP606: TP; TP-D1r0
U601, U602: TC358775XBG-BGA64
U603, U604: LT3495BEDDB#TRPBF; LT3495_DFN

Connections:
CTRL: R605.1, R606.1, U603.4 (CTRL), U604.4 (CTRL)
I2C_L_SCL: R624.1
I2C_L_SDA: R625.1
I2C_R_SCL: R626.1
I2C_R_SDA: R627.1
LLV1A: J601.31 (LV1A), U602.F7 (LVTX1DP)
LLV1B: J601.32 (LV1B), U602.F8 (LVTX1DN)
LLV2A: J601.33 (LV2A), U602.C7 (LVTX1AP)
LLV2B: J601.34 (LV2B), U602.C8 (LVTX1AN)
LLV3A: J601.35 (LV3A), U602.D7 (LVTX1BP)
LLV3B: J601.36 (LV3B), U602.D8 (LVTX1BN)
LLV4A: J601.37 (LV4A), U602.E7 (LVTX1CP)
LLV4B: J601.38 (LV4A), U602.E8 (LVTX1CN)
LLV5A: J601.39 (LV5A), U602.G7 (LVTX1EP)
LLV5B: J601.40 (LV5B), U602.G8 (LVTX1EN)
LLV6A: J601.53 (LV6A), U602.B2 (LVTX2AP)
LLV6B: J601.54 (LV6B), U602.A2 (LVTX2AN)
LLV7A: J601.51 (LV7A), U602.B3 (LVTX2BP)
LLV7B: J601.52 (LV7B), U602.A3 (LVTX2BN)
LLV8A: J601.49 (LV8A), U602.B4 (LVTX2CP)
LLV8B: J601.50 (LV8B), U602.A4 (LVTX2CN)
LLV9A: J601.47 (LV9A), U602.B6 (LVTX2EP)
LLV9B: J601.48 (LV9B), U602.A6 (LVTX2EN)
LLV10A: J601.55 (LV10A), U602.B5 (LVTX2DP)
LLV10B: J601.56 (LV10B), U602.A5 (LVTX2DN)
L_LCD_VCCP: C635.2, C648.2, J601.3 (VCCP_O), J601.4 (VCCP_I), J601.5 (VCCP_I), J601.78 (VCCP_I), J601.79 (VCCP_I)
L_VDD1_1V8: C637.2, C642.2, J601.12 (VDD1_1V8), J601.13 (VDD1_1V8), J601.63 (VDD1_1V8), J601.64 (VDD1_1V8), R614.1, R615.1
unnamed: C601.1, C602.1, L601.1, U603.3 (VCC)
unnamed: C601.2, C602.2
unnamed: C603.1, D601.2, U603.8 (CAP), U603.9 (CAP)
unnamed: C604.1, R610.2, U603.7 (VOUT)
unnamed: C605.1, C606.1, L602.1, U604.3 (VCC)
unnamed: C605.2, C606.2
unnamed: C607.1, D602.2, U604.8 (CAP), U604.9 (CAP)
unnamed: C608.1, R608.2, U604.7 (VOUT)
unnamed: C609.1, C610.1, C611.1, C612.1
unnamed: C609.2, C610.2, C611.2, C612.2
unnamed: C613.1, C614.1, C615.1, C616.1, C617.1, C618.1
unnamed: C613.2, C614.2, C615.2, C616.2, C617.2, C618.2
unnamed: C619.1, C620.1, C621.1, C622.1, C623.1, C624.1
unnamed: C619.2, C620.2, C621.2, C622.2, C623.2, C624.2
unnamed: C625.1, C626.1, C627.1, C628.1, C629.1, R602.1
unnamed: C625.2, C626.2, C627.2, C628.2, C629.2
unnamed: C630.1, C631.1, C632.1, C633.1, C634.1, R601.1
unnamed: C630.2, C631.2, C632.2, C633.2, C634.2
unnamed: C636.2, J601.6 (VDD), J601.7 (VDD)
unnamed: C638.2, J601.27 (VDD1IF_1V8)
unnamed: C639.1, J601.41 (VDD1IF_1V8)
unnamed: C639.2, J601.42 (VSSIF), J601.43 (GND), J601.44 (GND), J601.45 (VSSIF)
unnamed: C640.2, J601.46 (VDD1IF_1V8)
unnamed: C641.1, J601.60 (VDD1IF)
unnamed: C641.2, J601.57 (GND), J601.58 (GND), J601.59 (VSSIF), J601.62 (GND)
unnamed: C643.1, C644.1, C645.1, C646.1, C647.1, R628.1
unnamed: C643.2, J601.68 (VCAL)
unnamed: C644.2, J601.70 (VREF)
unnamed: C645.2, J601.71 (VG255)
unnamed: C646.2, J601.72 (VG0)
unnamed: C647.2, J601.73 (VOFS)
unnamed: C650.2, J602.6 (VDD), J602.7 (VDD)
unnamed: C652.2, J602.27 (VDD1IF_1V8)
unnamed: C653.1, J602.41 (VDD1IF_1V8)
unnamed: C653.2, J602.42 (VSSIF), J602.43 (GND), J602.44 (GND), J602.45 (VSSIF)
unnamed: C654.2, J602.46 (VDD1IF_1V8)
unnamed: C655.1, J602.60 (VDD1IF)
unnamed: C655.2, J602.57 (GND), J602.58 (GND), J602.59 (VSSIF), J602.62 (GND)
unnamed: C657.1, C658.1, C659.1, C660.1, C661.1, R622.1
unnamed: C657.2, J602.68 (VCAL)
unnamed: C658.2, J602.70 (VREF)
unnamed: C659.2, J602.71 (VG255)
unnamed: C660.2, J602.72 (VG0)
unnamed: C661.2, J602.73 (VOFS)
unnamed: D601.1, L601.2, U603.10 (SW)
unnamed: D602.1, L602.2, U604.10 (SW)
unnamed: J601.1 (VCATH), J601.2 (VCATH)
unnamed: J601.8 (VSS), J601.9 (VSS), J601.10 (VSS), J601.11 (VSS)
unnamed: J601.14 (XCS), R623.1
unnamed: J601.15 (XSCK), R611.1
unnamed: J601.16 (SI), R612.1
unnamed: J601.17 (SO), R613.1
unnamed: J601.18 (PSCNT), J601.21 (GND), J601.22 (GND), J601.23 (GND), J601.24 (GND), J601.25 (GND)
unnamed: J601.19 (XCLR), TP605.1
unnamed: J601.28 (VSSIF), J601.29 (GND), J601.30 (GND)
unnamed: J601.65 (VSS), J601.66 (VSS), J601.67 (GND)
unnamed: J601.69 (R_IB), R628.2
unnamed: J601.74 (VSS), J601.75 (VSS)
unnamed: J601.76 (VDD2), J601.77 (VDD2)
unnamed: J601.80 (VCATH), J601.81 (VCATH)
unnamed: J602.1 (VCATH), J602.2 (VCATH)
unnamed: J602.8 (VSS), J602.9 (VSS), J602.10 (VSS), J602.11 (VSS)
unnamed: J602.14 (XCS), R618.1
unnamed: J602.15 (XSCK), R619.1
unnamed: J602.16 (SI), R620.1
unnamed: J602.17 (SO), R621.1
unnamed: J602.18 (PSCNT), J602.21 (GND), J602.22 (GND), J602.23 (GND), J602.24 (GND), J602.25 (GND)
unnamed: J602.19 (XCLR), TP606.1
unnamed: J602.28 (VSSIF), J602.29 (GND), J602.30 (GND)
unnamed: J602.65 (VSS), J602.66 (VSS), J602.67 (GND)
unnamed: J602.69 (R_IB), R622.2
unnamed: J602.74 (VSS), J602.75 (VSS)
unnamed: J602.76 (VDD2), J602.77 (VDD2)
unnamed: J602.80 (VCATH), J602.81 (VCATH)
unnamed: R607.2, U604.5 (~\\\\\SHDN)
unnamed: R608.1, U604.6 (FB)
unnamed: R609.2, U603.5 (~\\\\\SHDN)
unnamed: R610.1, U603.6 (FB)
unnamed: R624.2, R625.2, R626.2, R627.2
unnamed: R631.1, U602.G1 (I2C_SCL)
unnamed: R632.1, U602.H1 (I2C_SDA)
unnamed: R684.1, U601.D5 (TM)
unnamed: R694.1, U602.D5 (TM)
unnamed: TP601.1, U601.C3 (STBY)
unnamed: TP602.1, U601.D4 (RESX)
unnamed: TP603.1, U602.C3 (STBY)
unnamed: TP604.1, U602.D4 (RESX)
unnamed: U601.A1 (VSS_LVDS2_12), U601.A7 (VSS_LVDS2_18), U601.A8 (VSS_LVDS1_12), U601.C1 (VSSIO), U601.C6 (VSS_LVDS1_18), U601.E1 (VSSC), U601.E5 (VSSC), U601.E6 (VSS_LVDS1_12), U601.F1 (VSSIO), U601.F4 (VSS_MIPI), U601.F5 (VSS_MIPI), U601.H8 (VSS_LVDS1_18)
unnamed: U601.B1 (VDD_LVDS2_12), U601.B8 (VDD_LVDS1_12)
unnamed: U601.B7 (VDD_LVDS2_18), U601.C5 (VDD_LVDS2_18), U601.D6 (VDD_LVDS1_18), U601.H7 (VDD_LVDS1_18)
unnamed: U601.C2 (VDDIO), U601.F2 (VDDIO)
unnamed: U601.E2 (VDDC), U601.E4 (VDDC)
unnamed: U601.F3 (VDD_MIPI), U601.F6 (VDD_MIPI)
unnamed: U602.A1 (VSS_LVDS2_12), U602.A7 (VSS_LVDS2_18), U602.A8 (VSS_LVDS1_12), U602.C1 (VSSIO), U602.C6 (VSS_LVDS1_18), U602.E1 (VSSC), U602.E5 (VSSC), U602.E6 (VSS_LVDS1_12), U602.F1 (VSSIO), U602.F4 (VSS_MIPI), U602.F5 (VSS_MIPI), U602.H8 (VSS_LVDS1_18)
unnamed: U602.B1 (VDD_LVDS2_12), U602.B8 (VDD_LVDS1_12)
unnamed: U602.B7 (VDD_LVDS2_18), U602.C5 (VDD_LVDS2_18), U602.D6 (VDD_LVDS1_18), U602.H7 (VDD_LVDS1_18)
unnamed: U602.C2 (VDDIO), U602.F2 (VDDIO)
unnamed: U602.E2 (VDDC), U602.E4 (VDDC)
unnamed: U602.F3 (VDD_MIPI), U602.F6 (VDD_MIPI)
unnamed: U603.1 (GND), U603.2 (GND), U603.11 (GND)
unnamed: U604.1 (GND), U604.2 (GND), U604.11 (GND)
RLV1A: J602.31 (LV1A), U601.F7 (LVTX1DP)
RLV1B: J602.32 (LV1B), U601.F8 (LVTX1DN)
RLV2A: J602.33 (LV2A), U601.C7 (LVTX1AP)
RLV2B: J602.34 (LV2B), U601.C8 (LVTX1AN)
RLV3A: J602.35 (LV3A), U601.D7 (LVTX1BP)
RLV3B: J602.36 (LV3B), U601.D8 (LVTX1BN)
RLV4A: J602.37 (LV4A), U601.E7 (LVTX1CP)
RLV4B: J602.38 (LV4A), U601.E8 (LVTX1CN)
RLV5A: J602.39 (LV5A), U601.G7 (LVTX1EP)
RLV5B: J602.40 (LV5B), U601.G8 (LVTX1EN)
RLV6A: J602.53 (LV6A), U601.B2 (LVTX2AP)
RLV6B: J602.54 (LV6B), U601.A2 (LVTX2AN)
RLV7A: J602.51 (LV7A), U601.B3 (LVTX2BP)
RLV7B: J602.52 (LV7B), U601.A3 (LVTX2BN)
RLV8A: J602.49 (LV8A), U601.B4 (LVTX2CP)
RLV8B: J602.50 (LV8B), U601.A4 (LVTX2CN)
RLV9A: J602.47 (LV9A), U601.B6 (LVTX2EP)
RLV9B: J602.48 (LV9B), U601.A6 (LVTX2EN)
RLV10A: J602.55 (LV10A), U601.B5 (LVTX2DP)
RLV10B: J602.56 (LV10B), U601.A5 (LVTX2DN)
R_I2C_SCL: R629.1, R633.1, U601.G1 (I2C_SCL)
R_I2C_SDA: R630.1, R634.1, U601.H1 (I2C_SDA)
R_LCD_VCCP: C649.2, C662.2, J602.3 (VCCP_O), J602.4 (VCCP_I), J602.5 (VCCP_I), J602.78 (VCCP_I), J602.79 (VCCP_I)
R_VDD1_1V8: C651.2, C656.2, J602.12 (VDD1_1V8), J602.13 (VDD1_1V8), J602.63 (VDD1_1V8), J602.64 (VDD1_1V8), R616.1, R617.1

Notes on the sheet:
R Boost Voltgage
L Boost Voltgage
L LCD
R LCD
MIPI to Dual LVDS
