state-of-the-art/binocular/design/prototype_1/kicad/prototype_testboard-1/07_LT7911D.kicad_sch

## KiCad design design/prototype_1/kicad/prototype_testboard-1/07_LT7911D.kicad_sch (2022-01-14)

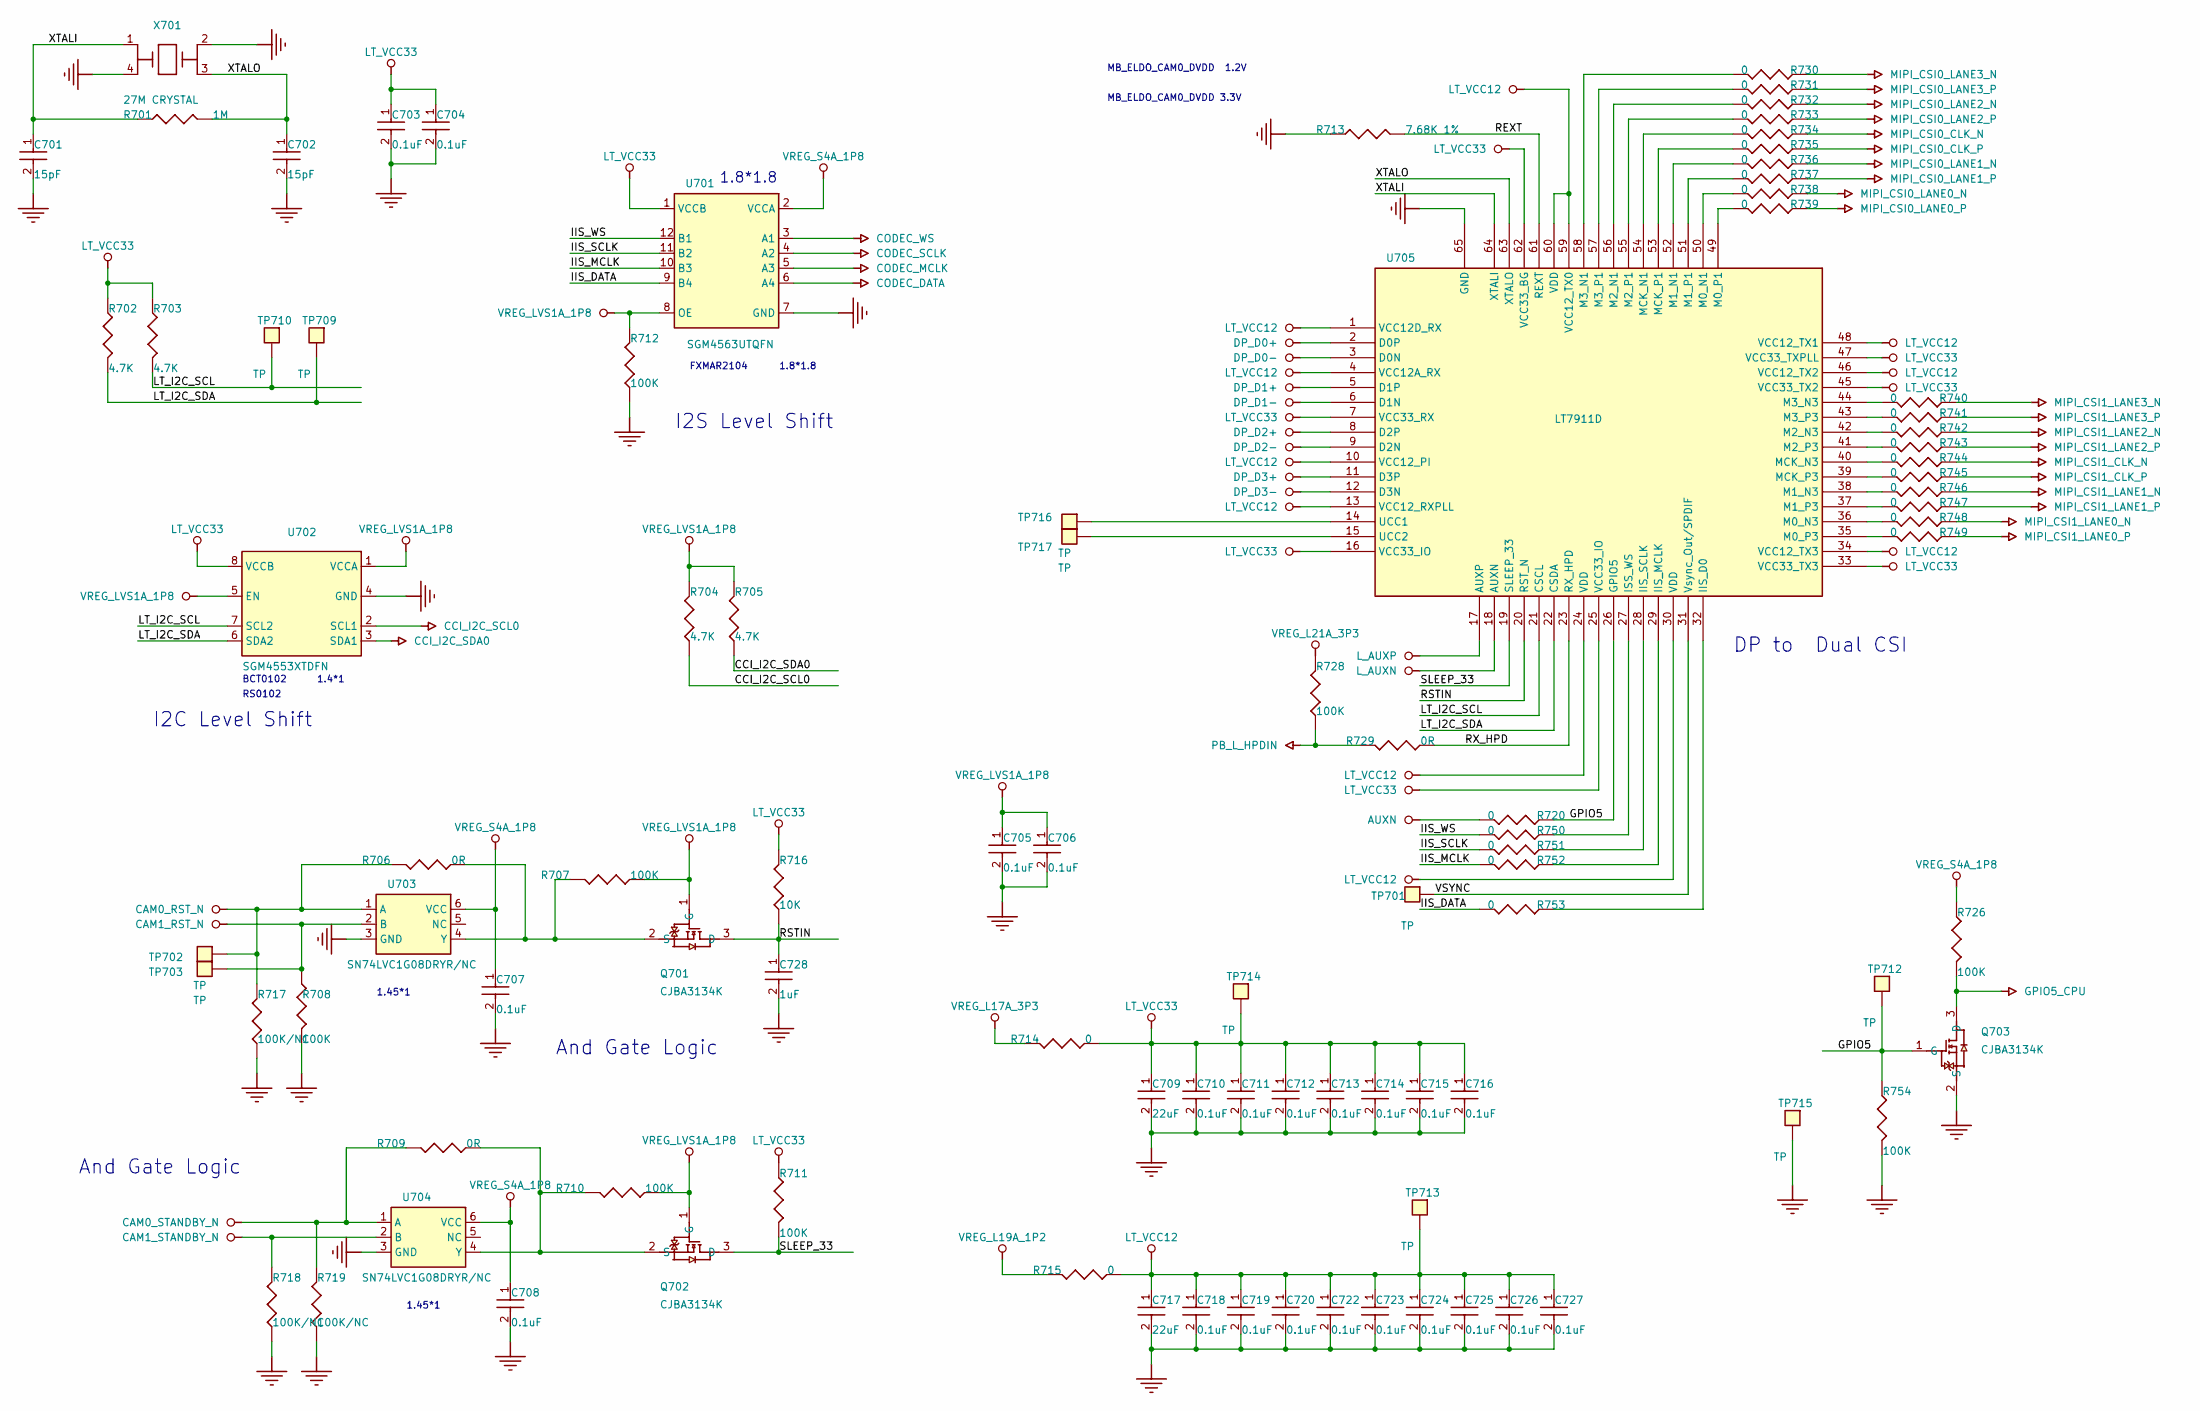
[picture p29: schematic 07_LT7911D.kicad_sch]

Parts:
C701, C702: 15pF; C0201
C703, C704, C705, C706, C707, C708, C710, C711, C712, C713, C714, C715, C716, C718, C719, C720, C722, C723, C724, C725, C726, C727: 0.1uF; C0201
C709, C717: 22uF; C0201
C728: 1uF; C0201
Q701, Q702, Q703: CJBA3134K; DFN1006-3L
R701: 1M; R0201
R702, R703, R704, R705: 4.7K; R0201
R706, R709, R729: 0R; R0201
R707, R708, R710, R711, R712, R726, R728, R754: 100K; R0201
R713: 7.68K 1%; R0201
R714, R720, R730, R731, R732, R733, R734, R735, R736, R737, R738, R739, R740, R741, R742, R743, R744, R745, R746, R747, R748, R749, R750, R751, R752, R753: 0; R0201
R715: 0; R0402
R716: 10K; R0201
R717, R718, R719: 100K/NC; R0201
TP701, TP702, TP703, TP709, TP710, TP712, TP713, TP714, TP715, TP716, TP717: TP; TP-D1r0
U701: SGM4563UTQFN; SGM4563_UTQFN
U702: SGM4553XTDFN; SGM4553_XTDFN_8L
U703, U704: SN74LVC1G08DRYR/NC; SON6_1r45_1mm
U705: LT7911D; LT7911D_QFN64
X701: 27M CRYSTAL; CRY2520

Connections:
CCI_I2C_SCL0: R704.1
CCI_I2C_SDA0: R705.1
GPIO5: Q703.1 (G), R720.2, R754.1, TP712.1, U705.26 (GPIO5)
IIS_DATA: R753.1, U701.9 (B4)
IIS_MCLK: R752.1, U701.10 (B3)
IIS_SCLK: R751.1, U701.11 (B2)
IIS_WS: R750.1, U701.12 (B1)
LT_I2C_SCL: R703.1, TP710.1, U702.7 (SCL2), U705.21 (CSCL)
LT_I2C_SDA: R702.1, TP709.1, U702.6 (SDA2), U705.22 (CSDA)
unnamed: C703.1, C704.1
unnamed: C703.2, C704.2
unnamed: C705.1, C706.1
unnamed: C705.2, C706.2
unnamed: C707.1, U703.6 (VCC)
unnamed: C708.1, U704.6 (VCC)
unnamed: C709.1, C710.1, C711.1, C712.1, C713.1, C714.1, C715.1, C716.1, R714.1, TP714.1
unnamed: C709.2, C710.2, C711.2, C712.2, C713.2, C714.2, C715.2, C716.2
unnamed: C717.1, C718.1, C719.1, C720.1, C722.1, C723.1, C724.1, C725.1, C726.1, C727.1, R715.1, TP713.1
unnamed: C717.2, C718.2, C719.2, C720.2, C722.2, C723.2, C724.2, C725.2, C726.2, C727.2
unnamed: Q701.1 (G), R707.1
unnamed: Q701.2 (S), R706.1, R707.2, U703.4 (Y)
unnamed: Q702.1 (G), R710.1
unnamed: Q702.2 (S), R709.1, R710.2, U704.4 (Y)
unnamed: Q703.3 (D), R726.2
unnamed: R702.2, R703.2
unnamed: R704.2, R705.2
unnamed: R706.2, R717.2, TP702.1, U703.1 (A)
unnamed: R708.1, TP703.1, U703.2 (B)
unnamed: R709.2, R719.2, U704.1 (A)
unnamed: R712.2, U701.8 (OE)
unnamed: R718.2, U704.2 (B)
unnamed: R728.1, R729.2
unnamed: R730.1, U705.58 (M3_N1)
unnamed: R731.1, U705.57 (M3_P1)
unnamed: R732.1, U705.56 (M2_N1)
unnamed: R733.1, U705.55 (M2_P1)
unnamed: R734.1, U705.54 (MCK_N1)
unnamed: R735.1, U705.53 (MCK_P1)
unnamed: R736.1, U705.52 (M1_N1)
unnamed: R737.1, U705.51 (M1_P1)
unnamed: R738.1, U705.50 (M0_N1)
unnamed: R739.1, U705.49 (M0_P1)
unnamed: R740.1, U705.44 (M3_N3)
unnamed: R741.1, U705.43 (M3_P3)
unnamed: R742.1, U705.42 (M2_N3)
unnamed: R743.1, U705.41 (M2_P3)
unnamed: R744.1, U705.40 (MCK_N3)
unnamed: R745.1, U705.39 (MCK_P3)
unnamed: R746.1, U705.38 (M1_N3)
unnamed: R747.1, U705.37 (M1_P3)
unnamed: R748.1, U705.36 (M0_N3)
unnamed: R749.1, U705.35 (M0_P3)
unnamed: R750.2, U705.27 (ISS_WS)
unnamed: R751.2, U705.28 (IIS_SCLK)
unnamed: R752.2, U705.29 (IIS_MCLK)
unnamed: R753.2, U705.32 (IIS_D0)
unnamed: TP716.1, U705.14 (UCC1)
unnamed: TP717.1, U705.15 (UCC2)
unnamed: U705.59 (VCC12_TX0), U705.60 (VDD)
REXT: R713.2, U705.61 (REXT)
RSTIN: C728.1, Q701.3 (D), R716.1, U705.20 (RST_N)
RX_HPD: R729.1, U705.23 (RX_HPD)
SLEEP_33: Q702.3 (D), R711.2, U705.19 (SLEEP_33)
VSYNC: TP701.1, U705.31 (Vsync_Out/SPDIF)
XTALI: C701.1, R701.1, U705.64 (XTALI), X701.1
XTALO: C702.1, R701.2, U705.63 (XTALO), X701.3

Notes on the sheet:
MB_ELDO_CAM0_DVDD 3.3V
FXMAR2104
And Gate Logic
I2S Level Shift
1.45*1
1.8*1.8
1.4*1
BCT0102
I2C Level Shift
DP to Dual CSI
RS0102
MB_ELDO_CAM0_DVDD 1.2V
