state-of-the-art/binocular/design/prototype_1/kicad/prototype_testboard-1/08_TPS65988DJ.kicad_sch

## KiCad design design/prototype_1/kicad/prototype_testboard-1/08_TPS65988DJ.kicad_sch (2022-01-14)

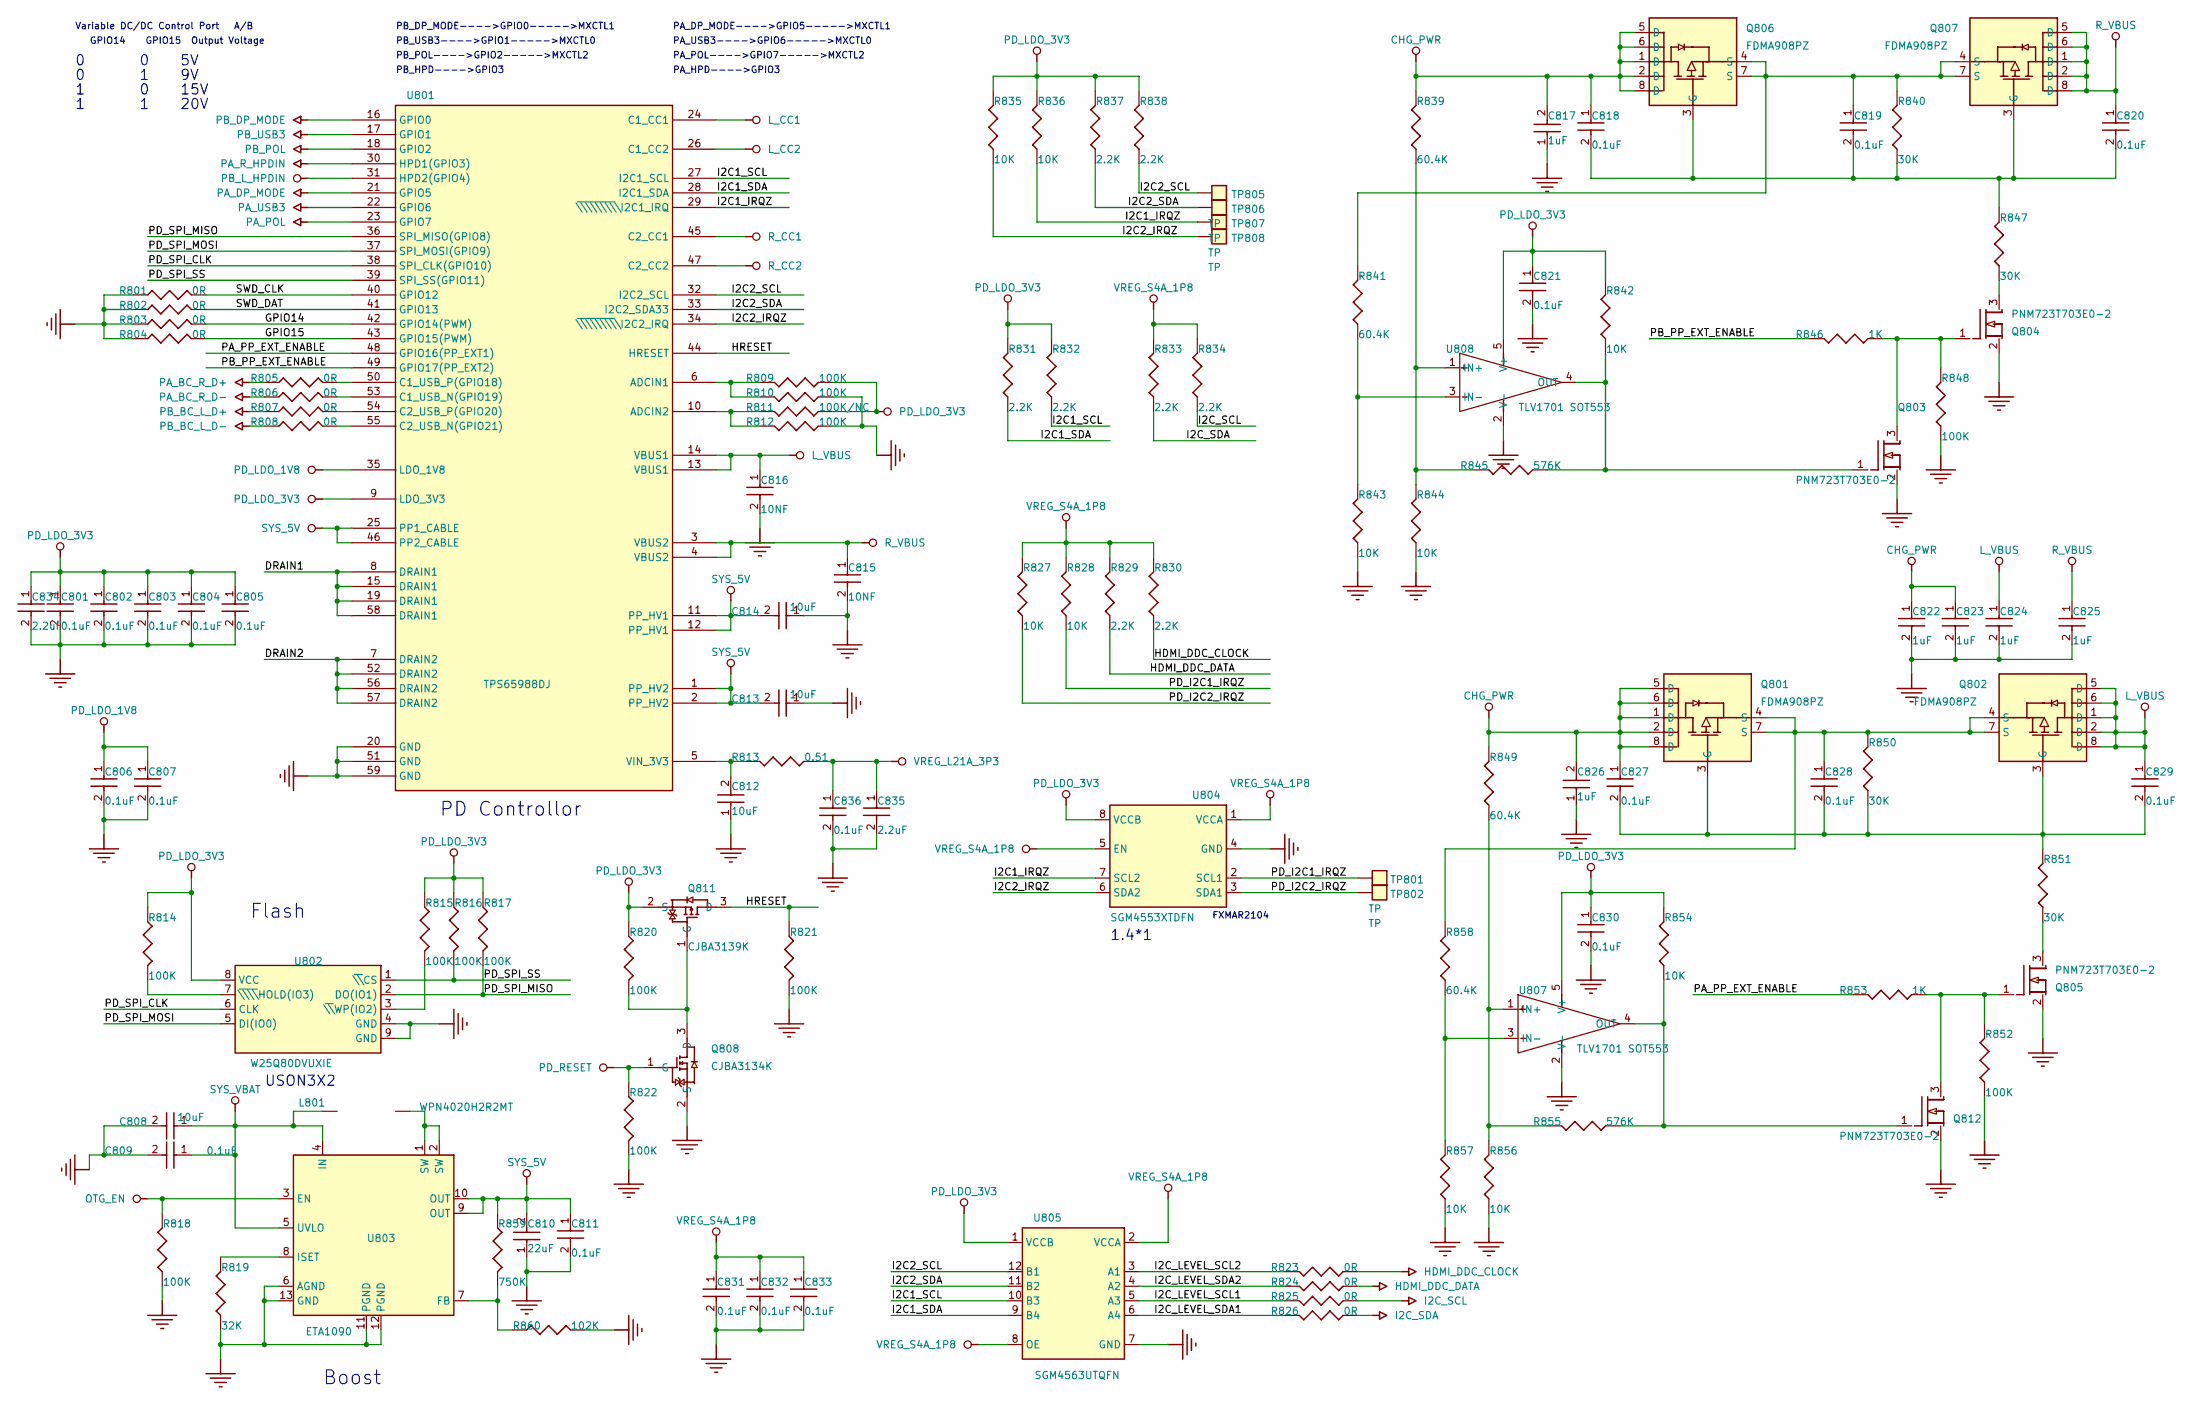
[picture p30: schematic 08_TPS65988DJ.kicad_sch]

Parts:
C801, C802, C803, C804, C805, C806, C807, C809, C811, C818, C819, C820, C821, C827, C828, C829, C830, C831, C832, C833, C836: 0.1uF; C0201
C808, C812, C813, C814: 10uF; C0603; PART TYPE 801
C810: 22uF; C0603; PART TYPE 801
C815, C816: 10NF; C0201
C817, C826: 1uF; C0402; PART TYPE 801
C822, C823, C824, C825: 1uF; C0201
C834, C835: 2.2uF; C0201
L801: WPN4020H2R2MT; L{slash}IND{slash}SMD{slash}2520
Q801, Q802, Q806, Q807: FDMA908PZ
Q803, Q804, Q805, Q812: PNM723T703E0-2; SOT_723
Q808: CJBA3134K; DFN1006-3L
Q811: CJBA3139K; DFN1006-3L
R801, R802, R803, R804, R805, R806, R807, R808, R823, R824, R825, R826: 0R; R0201
R809, R810, R812, R814, R815, R816, R817, R818, R820, R821, R822, R848, R852: 100K; R0201
R811: 100K/NC; R0201
R813: 0.51; R0402
R819: 32K; R0201
R827, R828, R835, R836, R842, R843, R844, R854, R856, R857: 10K; R0201
R829, R830, R831, R832, R833, R834, R837, R838: 2.2K; R0201
R839, R841, R849, R858: 60.4K; R0201
R840, R847, R850, R851: 30K; R0201
R845, R855: 576K; R0201
R846, R853: 1K; R0201
R859: 750K; R0201
R860: 102K; R0201
TP801, TP802, TP805, TP806, TP807, TP808: TP; TP-D1r0
U801: TPS65988DJ; TPS65988DJ_QFN56
U802: W25Q80DVUXIE; WSON_8_3X2
U803: ETA1090; DFN3x3-12
U804: SGM4553XTDFN; SGM4553_XTDFN_8L
U805: SGM4563UTQFN; SGM4563_UTQFN
U807, U808: TLV1701 SOT553; SOT553-5

Connections:
DRAIN1: U801.8 (DRAIN1), U801.15 (DRAIN1), U801.19 (DRAIN1), U801.58 (DRAIN1)
DRAIN2: U801.7 (DRAIN2), U801.52 (DRAIN2), U801.56 (DRAIN2), U801.57 (DRAIN2)
GPIO14: R803.2, U801.42 (GPIO14(PWM))
GPIO15: R804.2, U801.43 (GPIO15(PWM))
HDMI_DDC_CLOCK: R830.1
HDMI_DDC_DATA: R829.1
HRESET: Q811.3 (D), R821.1, U801.44 (HRESET)
I2C1_IRQZ: R836.1, TP807.1, U801.29 (~\\\\\\\\\I2C1_IRQ), U804.7 (SCL2)
I2C1_SCL: R832.1, U801.27 (I2C1_SCL), U805.10 (B3)
I2C1_SDA: R831.1, U801.28 (I2C1_SDA), U805.9 (B4)
I2C2_IRQZ: R835.1, TP808.1, U801.34 (~\\\\\\\\\I2C2_IRQ), U804.6 (SDA2)
I2C2_SCL: R838.1, TP805.1, U801.32 (I2C2_SCL), U805.12 (B1)
I2C2_SDA: R837.1, TP806.1, U801.33 (I2C2_SDA33), U805.11 (B2)
I2C_LEVEL_SCL1: R825.2, U805.5 (A3)
I2C_LEVEL_SCL2: R823.2, U805.3 (A1)
I2C_LEVEL_SDA1: R826.2, U805.6 (A4)
I2C_LEVEL_SDA2: R824.2, U805.4 (A2)
I2C_SCL: R834.1
I2C_SDA: R833.1
unnamed: C801.1, C802.1, C803.1, C804.1, C805.1, C834.1
unnamed: C801.2, C802.2, C803.2, C804.2, C805.2, C834.2
unnamed: C806.1, C807.1
unnamed: C806.2, C807.2
unnamed: C808.1, C809.1, L801.1, U803.4 (IN), U803.5 (UVLO)
unnamed: C808.2, C809.2
unnamed: C810.1, C811.2
unnamed: C810.2, C811.1, R859.1, U803.9 (OUT), U803.10 (OUT)
unnamed: C812.2, R813.2, U801.5 (VIN_3V3)
unnamed: C813.2, U801.1 (PP_HV2), U801.2 (PP_HV2)
unnamed: C814.1, C815.2
unnamed: C814.2, U801.11 (PP_HV1), U801.12 (PP_HV1)
unnamed: C815.1, U801.3 (VBUS2), U801.4 (VBUS2)
unnamed: C816.1, U801.13 (VBUS1), U801.14 (VBUS1)
unnamed: C817.2, C818.1, Q806.1 (D), Q806.2 (D), Q806.5 (D), Q806.6 (D), Q806.8 (D), R839.2
unnamed: C818.2, C819.2, C820.2, Q806.3 (G), Q807.3 (G), R840.1, R847.2
unnamed: C819.1, Q806.4 (S), Q806.7 (S), Q807.4 (S), Q807.7 (S), R840.2, R841.2
unnamed: C820.1, Q807.1 (D), Q807.2 (D), Q807.5 (D), Q807.6 (D), Q807.8 (D)
unnamed: C821.1, R842.2, U808.5 (V+)
unnamed: C822.1, C823.1
unnamed: C822.2, C823.2, C824.2, C825.2
unnamed: C826.2, C827.1, Q801.1 (D), Q801.2 (D), Q801.5 (D), Q801.6 (D), Q801.8 (D), R849.2
unnamed: C827.2, C828.2, C829.2, Q801.3 (G), Q802.3 (G), R850.1, R851.2
unnamed: C828.1, Q801.4 (S), Q801.7 (S), Q802.4 (S), Q802.7 (S), R850.2, R858.2
unnamed: C829.1, Q802.1 (D), Q802.2 (D), Q802.5 (D), Q802.6 (D), Q802.8 (D)
unnamed: C830.1, R854.2, U807.5 (V+)
unnamed: C831.1, C832.1, C833.1
unnamed: C831.2, C832.2, C833.2
unnamed: C835.1, C836.1, R813.1
unnamed: C835.2, C836.2
unnamed: L801.2, U803.1 (SW), U803.2 (SW)
unnamed: Q803.1 (G), R842.1, R845.1, U808.4 (OUT)
unnamed: Q803.3 (DRAIN), Q804.1 (G), R846.1, R848.2
unnamed: Q804.3 (DRAIN), R847.1
unnamed: Q805.1 (G), Q812.3 (DRAIN), R852.2, R853.1
unnamed: Q805.3 (DRAIN), R851.1
unnamed: Q808.1 (G), R822.1
unnamed: Q808.3 (D), Q811.1 (G), R820.2
unnamed: Q811.2 (S), R820.1
unnamed: Q812.1 (G), R854.1, R855.1, U807.4 (OUT)
unnamed: R801.1, R802.1, R803.1, R804.1
unnamed: R805.2, U801.50 (C1_USB_P(GPIO18))
unnamed: R806.2, U801.53 (C1_USB_N(GPIO19))
unnamed: R807.2, U801.54 (C2_USB_P(GPIO20))
unnamed: R808.2, U801.55 (C2_USB_N(GPIO21))
unnamed: R809.1, R811.1
unnamed: R809.2, R810.2, U801.6 (ADCIN1)
unnamed: R810.1, R812.1
unnamed: R811.2, R812.2, U801.10 (ADCIN2)
unnamed: R814.1, U802.8 (VCC)
unnamed: R814.2, U802.7 (~\\\\HOLD(IO3))
unnamed: R815.1, R816.1, R817.1
unnamed: R815.2, U802.3 (~\\WP(IO2))
unnamed: R818.2, U803.3 (EN)
unnamed: R819.1, U803.6 (AGND), U803.11 (PGND), U803.12 (PGND), U803.13 (GND)
unnamed: R819.2, U803.8 (ISET)
unnamed: R827.2, R828.2, R829.2, R830.2
unnamed: R831.2, R832.2
unnamed: R833.2, R834.2
unnamed: R835.2, R836.2, R837.2, R838.2
unnamed: R839.1, R844.2, R845.2, U808.1 (IN+)
unnamed: R841.1, R843.2, U808.3 (IN-)
unnamed: R849.1, R855.2, R856.2, U807.1 (IN+)
unnamed: R857.2, R858.1, U807.3 (IN-)
unnamed: R859.2, R860.1, U803.7 (FB)
unnamed: U801.20 (GND), U801.51 (GND), U801.59 (GND)
unnamed: U801.25 (PP1_CABLE), U801.46 (PP2_CABLE)
unnamed: U802.4 (GND), U802.9 (GND)
PA_PP_EXT_ENABLE: R853.2, U801.48 (GPIO16(PP_EXT1))
PB_PP_EXT_ENABLE: R846.2, U801.49 (GPIO17(PP_EXT2))
PD_I2C1_IRQZ: R828.1, TP801.1, U804.2 (SCL1)
PD_I2C2_IRQZ: R827.1, TP802.1, U804.3 (SDA1)
PD_SPI_CLK: U801.38 (SPI_CLK(GPIO10)), U802.6 (CLK)
PD_SPI_MISO: R816.2, R817.2, U801.36 (SPI_MISO(GPIO8)), U801.39 (SPI_SS(GPIO11)), U802.1 (~\\CS), U802.2 (DO(IO1))
PD_SPI_MOSI: U801.37 (SPI_MOSI(GPIO9)), U802.5 (DI(IO0))
SWD_CLK: R801.2, U801.40 (GPIO12)
SWD_DAT: R802.2, U801.41 (GPIO13)

Notes on the sheet:
1 0 15V
Boost
Flash
PB_HPD---->GPIO3
Variable DC/DC Control Port A/B
USON3X2
0 0 5V
GPIO14 GPIO15 Output Voltage
PA_USB3---->GPIO6----->MXCTL0
1.4*1
PB_DP_MODE---->GPIO0----->MXCTL1
1 1 20V
PB_POL---->GPIO2----->MXCTL2
PD Controllor
FXMAR2104
PA_POL---->GPIO7----->MXCTL2
PB_USB3---->GPIO1----->MXCTL0
PA_DP_MODE---->GPIO5----->MXCTL1
0 1 9V
PA_HPD---->GPIO3
