state-of-the-art/binocular/design/prototype_1/kicad/prototype_testboard-1/09_BQ25616.kicad_sch

## KiCad design design/prototype_1/kicad/prototype_testboard-1/09_BQ25616.kicad_sch (2022-01-14)

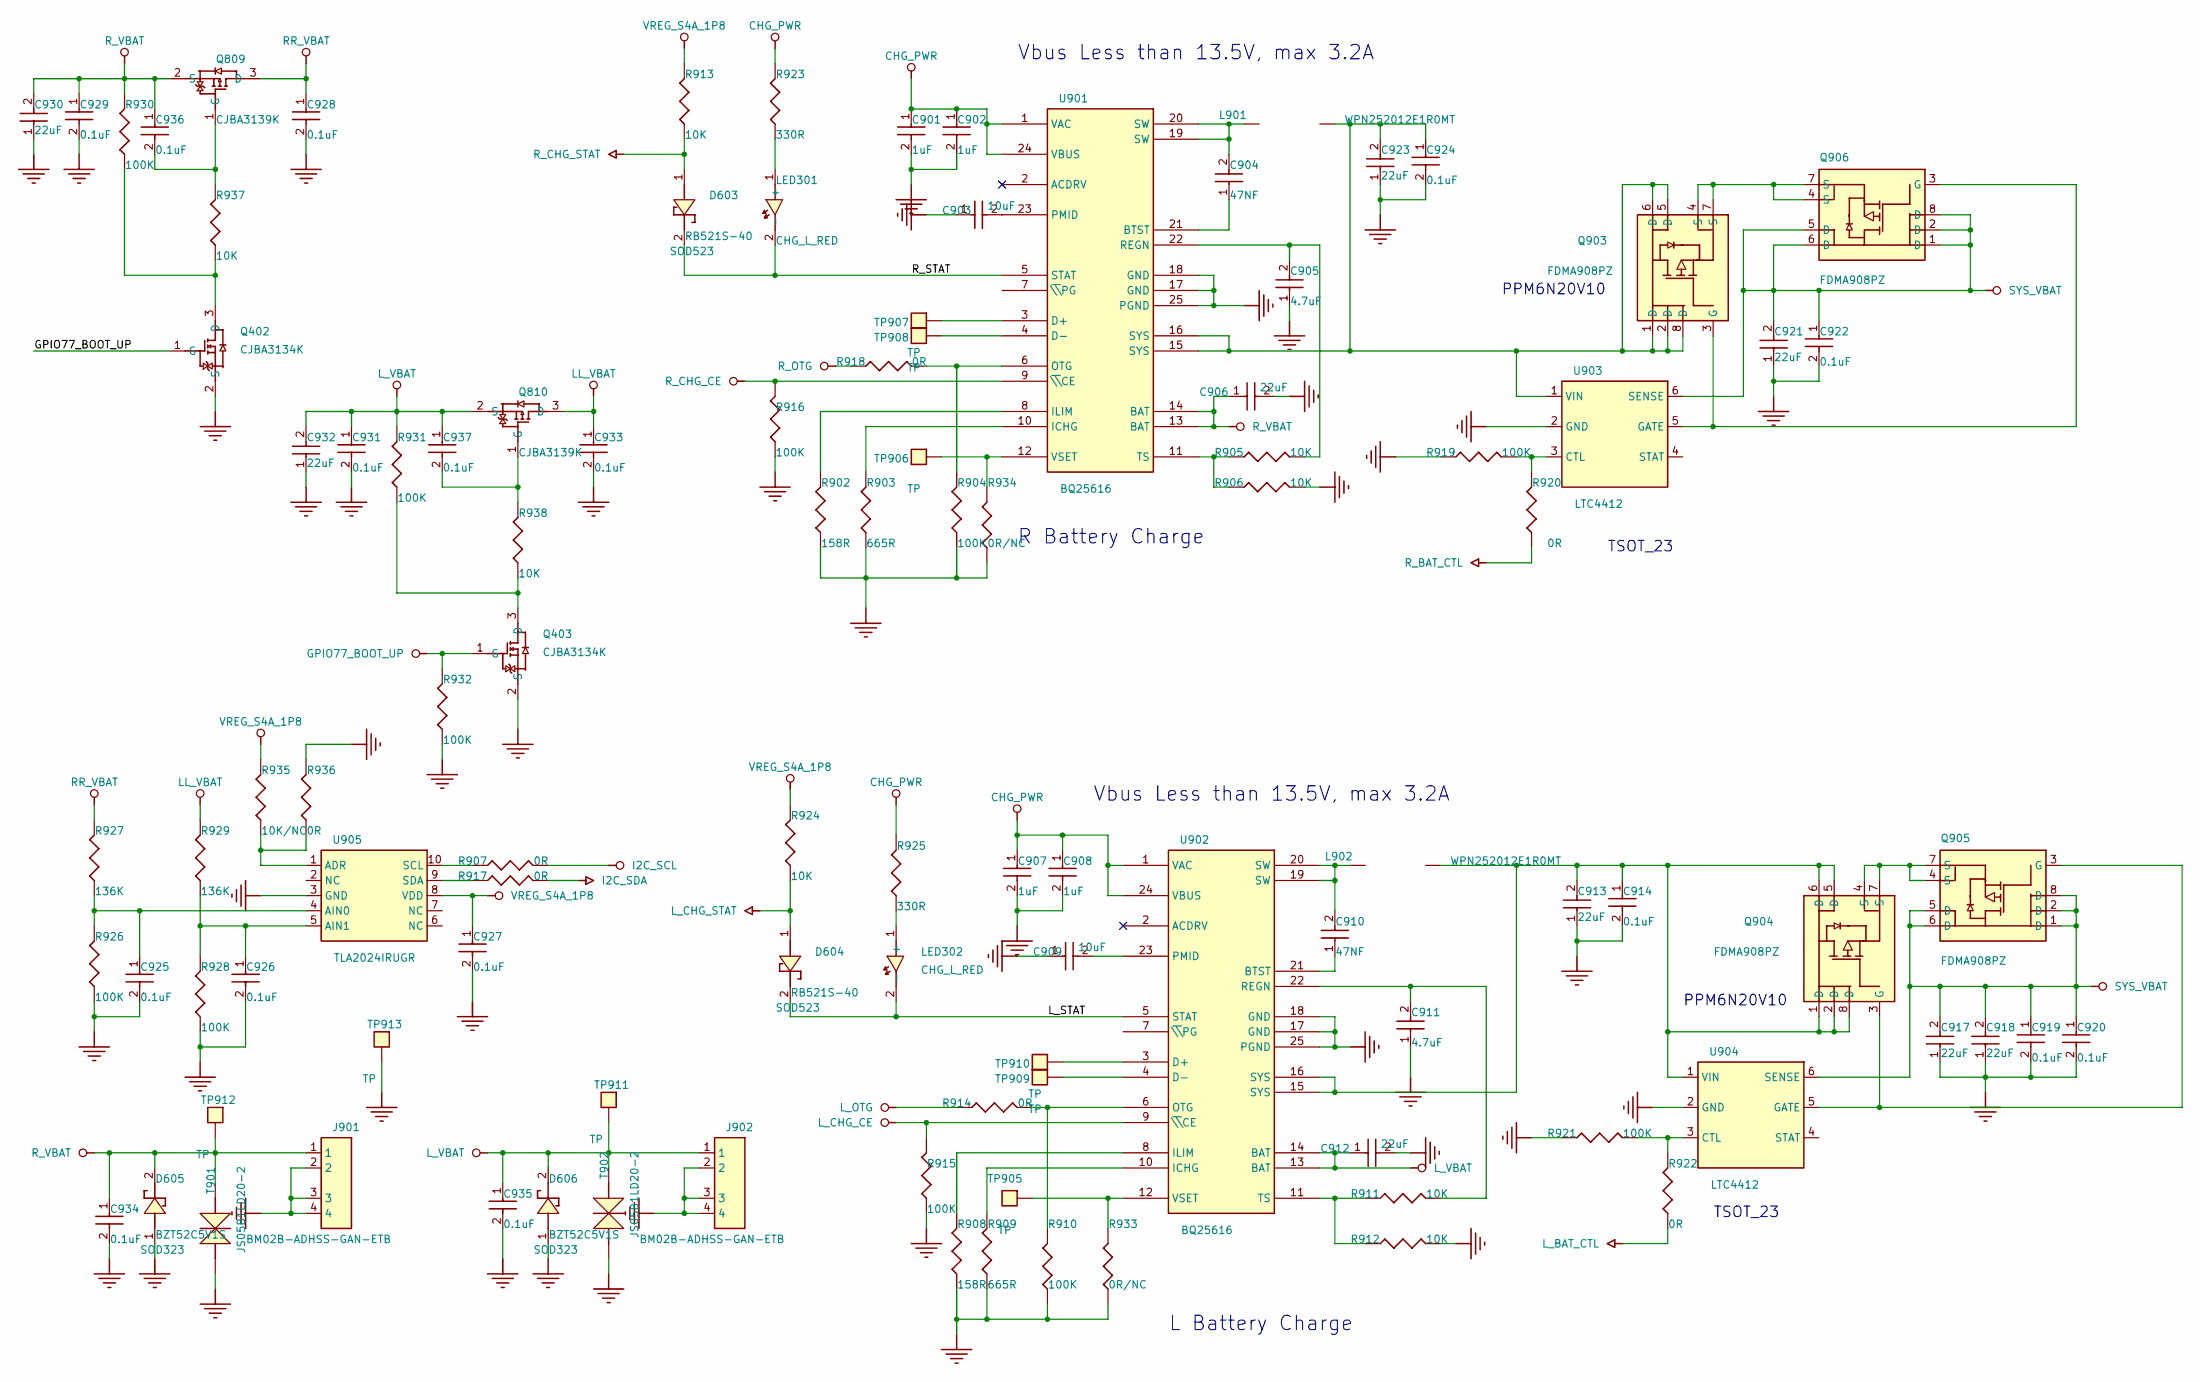
[picture p31: schematic 09_BQ25616.kicad_sch]

Parts:
C901, C902, C907, C908: 1uF; C0201
C903, C909: 10uF; C0603; PART TYPE 801
C904, C910: 47NF; C0201
C905, C911: 4.7uF; C0201
C906, C912, C913, C917, C918, C921, C923, C930, C932: 22uF; C0603; PART TYPE 801
C914, C919, C920, C922, C924, C925, C926, C927, C928, C929, C931, C933, C934, C935, C936, C937: 0.1uF; C0201
D603, D604: RB521S-40; DIODE{slash}DIP{slash}P10.0
D605, D606: BZT52C5V1S; DIODE{slash}DIP{slash}P10.0
J901, J902: BM02B-ADHSS-GAN-ETB; BM02B-ADHSS_2P
L901, L902: WPN252012E1R0MT; L{slash}IND{slash}SMD{slash}2520
LED301, LED302: CHG_L_RED; LED_0603
Q402, Q403: CJBA3134K; DFN1006-3L
Q809, Q810: CJBA3139K; DFN1006-3L
Q903, Q904, Q905, Q906: FDMA908PZ
R902, R908: 158R; R0201
R903, R909: 665R; R0201
R904, R910, R915, R916, R919, R921, R926, R928, R930, R931, R932: 100K; R0201
R905, R906, R911, R912, R913, R924, R937, R938: 10K; R0201
R907, R914, R917, R918, R920, R922, R936: 0R; R0201
R923, R925: 330R; R0201
R927, R929: 136K; R0201
R933, R934: 0R/NC; R0201
R935: 10K/NC; R0201
T901: JS05B1LD20-2; DFN1006-2; MANUFACTURER PART NUMBER RB551V-30TE-17
T902: JS05B1LD20-2; DFN1006-2; PART NUMBER TY01100606
TP905, TP906, TP907, TP908, TP909, TP910: TP; TP-D1r0
TP911, TP912, TP913: TP; TP-D2r0
U901, U902: BQ25616; BQ25616_WQFN24
U903, U904: LTC4412; TSOT-23-6
U905: TLA2024IRUGR; TLA2021_X2QFN

Connections:
GPIO77_BOOT_UP: Q402.1 (G)
L_STAT: D604.2, LED302.2 (-), U902.5 (STAT)
unnamed: C901.1, C902.1, U901.1 (VAC), U901.24 (VBUS)
unnamed: C901.2, C902.2
unnamed: C903.2, U901.23 (PMID)
unnamed: C904.1, U901.21 (BTST)
unnamed: C904.2, L901.1, U901.19 (SW), U901.20 (SW)
unnamed: C905.2, R905.2, U901.22 (REGN)
unnamed: C906.1, U901.13 (BAT), U901.14 (BAT)
unnamed: C907.1, C908.1, U902.1 (VAC), U902.24 (VBUS)
unnamed: C907.2, C908.2
unnamed: C909.2, U902.23 (PMID)
unnamed: C910.1, U902.21 (BTST)
unnamed: C910.2, L902.1, U902.19 (SW), U902.20 (SW)
unnamed: C911.2, R911.2, U902.22 (REGN)
unnamed: C912.1, U902.13 (BAT), U902.14 (BAT)
unnamed: C913.1, C914.2
unnamed: C913.2, C914.1, L902.2, Q904.1 (D), Q904.2 (D), Q904.5 (D), Q904.6 (D), Q904.8 (D), U902.15 (SYS), U902.16 (SYS), U904.1 (VIN)
unnamed: C917.1, C918.1, C919.2, C920.2
unnamed: C917.2, C918.2, C919.1, C920.1, Q905.1 (D), Q905.2 (D), Q905.5 (D), Q905.6 (D), Q905.8 (D), U904.6 (SENSE)
unnamed: C921.1, C922.2
unnamed: C921.2, C922.1, Q906.1 (D), Q906.2 (D), Q906.5 (D), Q906.6 (D), Q906.8 (D), U903.6 (SENSE)
unnamed: C923.1, C924.2
unnamed: C923.2, C924.1, L901.2, Q903.1 (D), Q903.2 (D), Q903.5 (D), Q903.6 (D), Q903.8 (D), U901.15 (SYS), U901.16 (SYS), U903.1 (VIN)
unnamed: C925.1, R926.1, R927.2, U905.4 (AIN0)
unnamed: C925.2, R926.2
unnamed: C926.1, R928.1, R929.2, U905.5 (AIN1)
unnamed: C926.2, R928.2
unnamed: C927.1, U905.8 (VDD)
unnamed: C928.1, Q809.3 (D)
unnamed: C929.1, C930.2, C936.1, Q809.2 (S), R930.1
unnamed: C931.1, C932.2, C937.1, Q810.2 (S), R931.1
unnamed: C933.1, Q810.3 (D)
unnamed: C934.1, D605.2, J901.1, T901.2 (-), TP912.1
unnamed: C935.1, D606.2, J902.1, T902.2 (-), TP911.1
unnamed: C936.2, Q809.1 (G), R937.1
unnamed: C937.2, Q810.1 (G), R938.1
unnamed: D603.1, R913.2
unnamed: D604.1, R924.2
unnamed: J901.2, J901.3, J901.4
unnamed: J902.2, J902.3, J902.4
unnamed: LED301.1 (+), R923.2
unnamed: LED302.1 (+), R925.2
unnamed: Q402.3 (D), R930.2, R937.2
unnamed: Q403.1 (G), R932.1
unnamed: Q403.3 (D), R931.2, R938.2
unnamed: Q903.3 (G), Q906.3 (G), U903.5 (GATE)
unnamed: Q903.4 (S), Q903.7 (S), Q906.4 (S), Q906.7 (S)
unnamed: Q904.3 (G), Q905.3 (G), U904.5 (GATE)
unnamed: Q904.4 (S), Q904.7 (S), Q905.4 (S), Q905.7 (S)
unnamed: R902.1, R903.1, R904.1, R934.1
unnamed: R902.2, U901.8 (ILIM)
unnamed: R903.2, U901.10 (ICHG)
unnamed: R904.2, R918.2, U901.6 (OTG)
unnamed: R905.1, R906.1, U901.11 (TS)
unnamed: R907.1, U905.10 (SCL)
unnamed: R908.1, R909.1, R910.1, R933.1
unnamed: R908.2, U902.8 (ILIM)
unnamed: R909.2, U902.10 (ICHG)
unnamed: R910.2, R914.2, U902.6 (OTG)
unnamed: R911.1, R912.1, U902.11 (TS)
unnamed: R915.2, U902.9 (~\\CE)
unnamed: R916.2, U901.9 (~\\CE)
unnamed: R917.1, U905.9 (SDA)
unnamed: R919.2, R920.2, U903.3 (CTL)
unnamed: R921.2, R922.2, U904.3 (CTL)
unnamed: R933.2, TP905.1, U902.12 (VSET)
unnamed: R934.2, TP906.1, U901.12 (VSET)
unnamed: R935.2, R936.2, U905.1 (ADR)
unnamed: TP907.1, U901.3 (D+)
unnamed: TP908.1, U901.4 (D-)
unnamed: TP909.1, U902.4 (D-)
unnamed: TP910.1, U902.3 (D+)
unnamed: U901.17 (GND), U901.18 (GND), U901.25 (PGND)
unnamed: U902.17 (GND), U902.18 (GND), U902.25 (PGND)
R_STAT: D603.2, LED301.2 (-), U901.5 (STAT)

Notes on the sheet:
R Battery Charge
PPM6N20V10
Vbus Less than 13.5V, max 3.2A
TSOT_23
L Battery Charge
