state-of-the-art/binocular/design/prototype_1/kicad/prototype_testboard-1/10_WM8998.kicad_sch

## KiCad design design/prototype_1/kicad/prototype_testboard-1/10_WM8998.kicad_sch (2022-01-14)

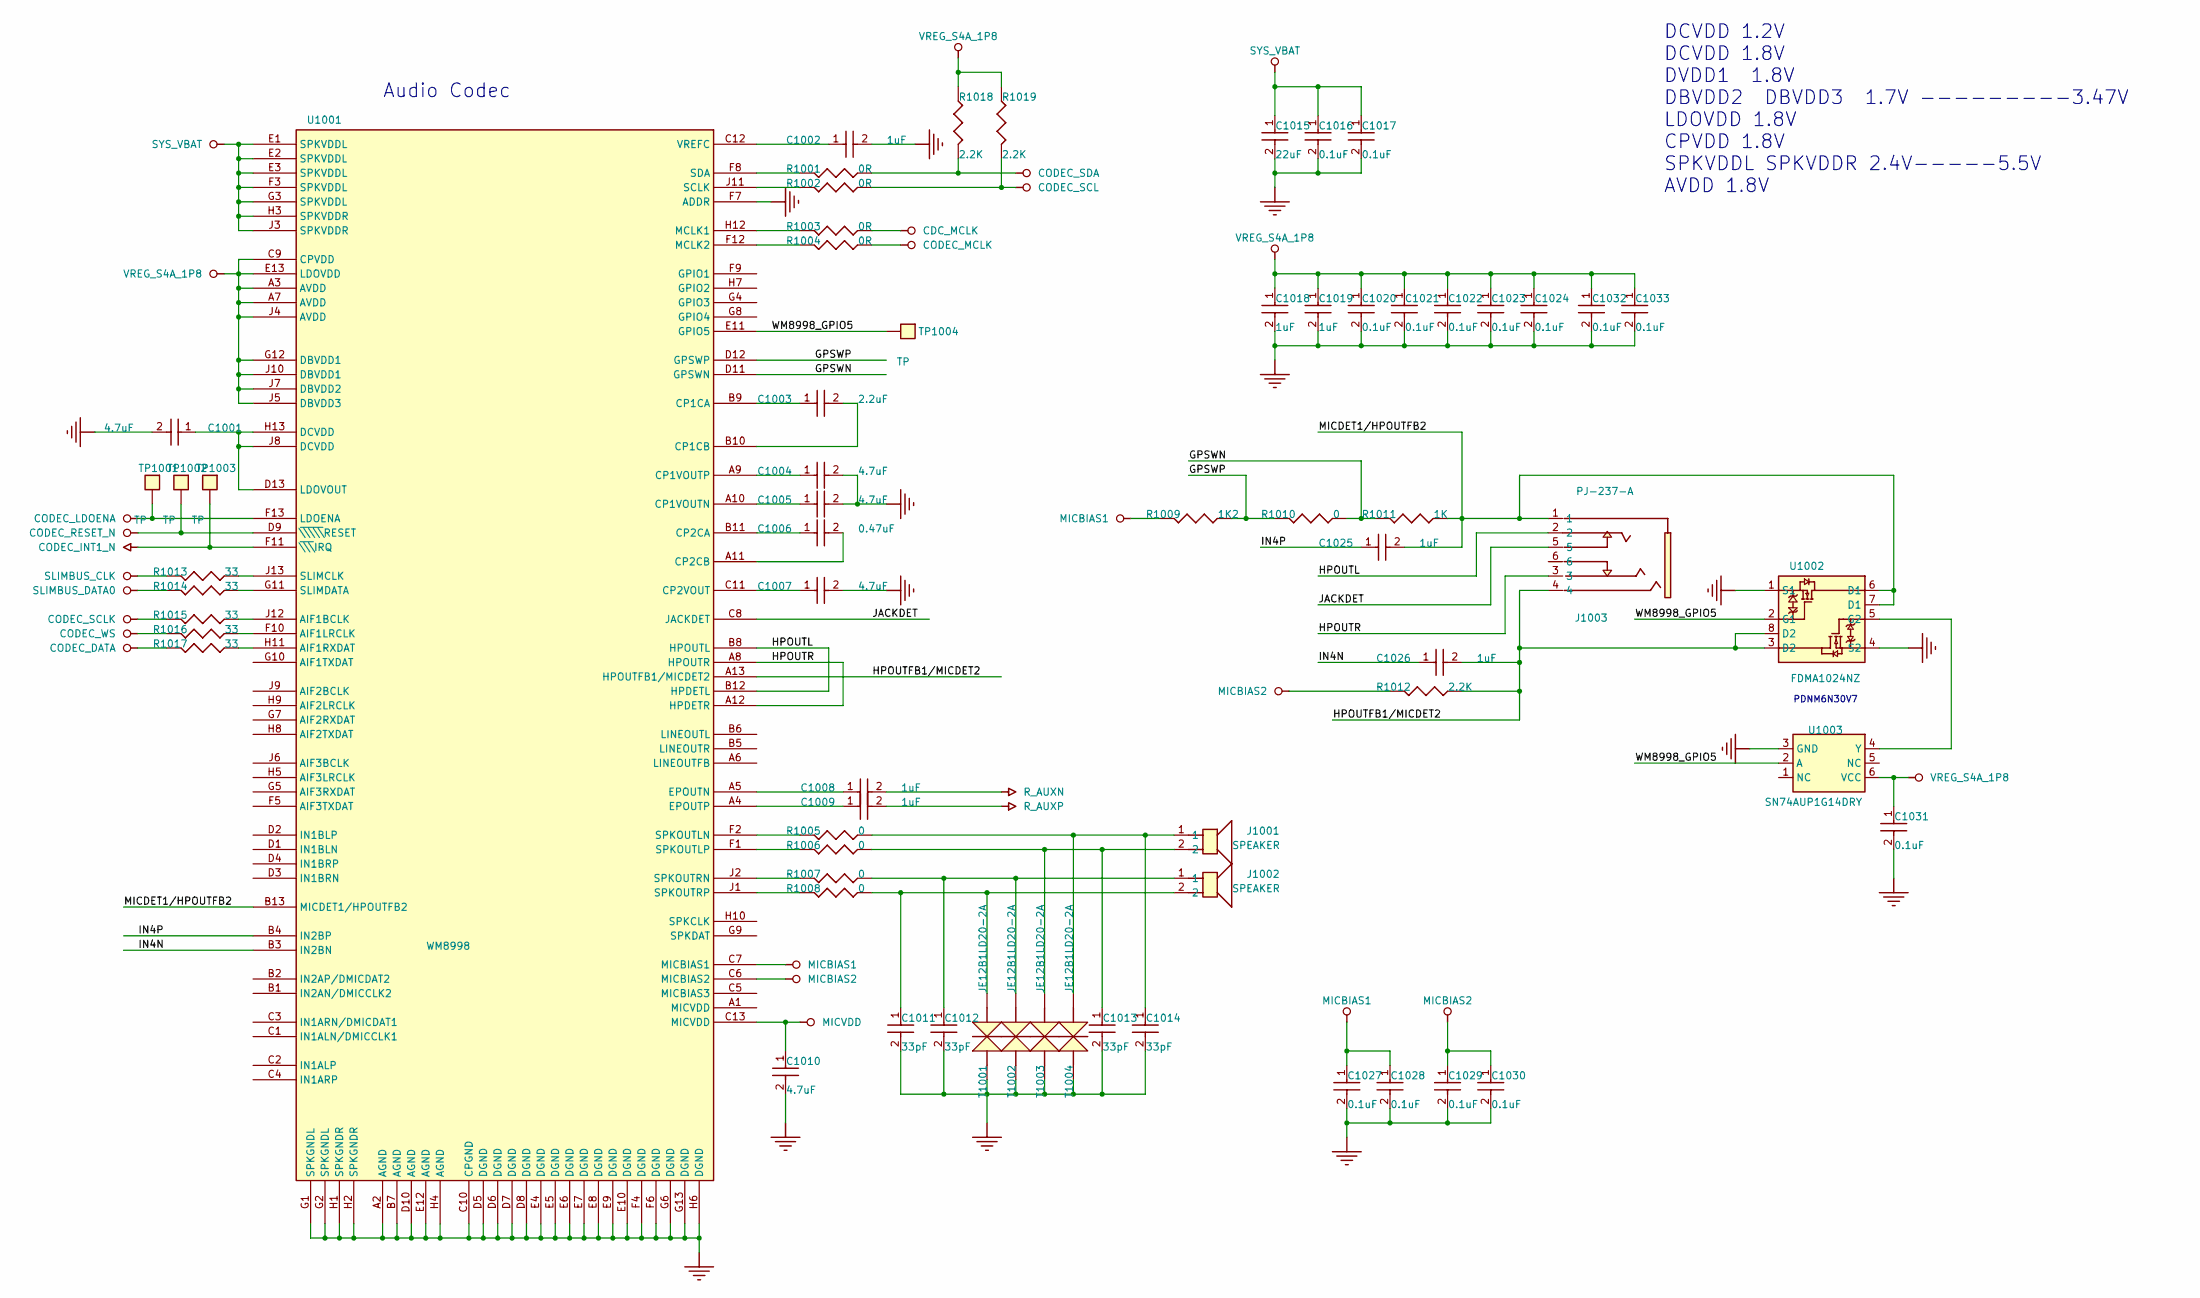
[picture p32: schematic 10_WM8998.kicad_sch]

Parts:
C1001, C1004, C1005, C1007, C1010: 4.7uF; C0201
C1002, C1008, C1009, C1018, C1019, C1025, C1026: 1uF; C0201
C1003: 2.2uF; C0201
C1006: 0.47uF; C0201
C1011, C1012, C1013, C1014: 33pF; C0201
C1015: 22uF; C0201
C1016, C1017, C1020, C1021, C1022, C1023, C1024, C1027, C1028, C1029, C1030, C1031, C1032, C1033: 0.1uF; C0201
J1001, J1002: SPEAKER; PAD_2P_4020
J1003: PJ-237-A
R1001, R1002, R1003, R1004: 0R; R0201
R1005, R1006, R1007, R1008: 0; R0402
R1009: 1K2; R0201
R1010: 0; R0201
R1011: 1K; R0201
R1012, R1018, R1019: 2.2K; R0201
R1013, R1014, R1015, R1016, R1017: 33; R0201
T1001, T1002, T1003, T1004: JE12B1LD20-2A; DFN1006-2; PART NUMBER TY01100606
TP1001, TP1002, TP1003, TP1004: TP; TP-D1r0
U1001: WM8998; WM8998_WCSP_117BALL
U1002: FDMA1024NZ
U1003: SN74AUP1G14DRY; SON6_1r45_1mm

Connections:
GPSWN: R1010.1, R1011.2, U1001.D11 (GPSWN)
GPSWP: R1009.1, R1010.2, U1001.D12 (GPSWP)
HPOUTFB1/MICDET2: C1026.2, J1003.4, R1012.1, U1001.A13 (HPOUTFB1/MICDET2), U1002.3 (D2), U1002.8 (D2)
HPOUTL: J1003.2, U1001.B8 (HPOUTL), U1001.B12 (HPDETL)
HPOUTR: J1003.3, U1001.A8 (HPOUTR), U1001.A12 (HPDETR)
IN4N: C1026.1, U1001.B3 (IN2BN)
IN4P: C1025.1, U1001.B4 (IN2BP)
JACKDET: J1003.5, U1001.C8 (JACKDET)
MICDET1/HPOUTFB2: C1025.2, J1003.1, R1011.1, U1001.B13 (MICDET1/HPOUTFB2), U1002.6 (D1), U1002.7 (D1)
unnamed: C1001.1, U1001.D13 (LDOVOUT), U1001.H13 (DCVDD), U1001.J8 (DCVDD)
unnamed: C1002.1, U1001.C12 (VREFC)
unnamed: C1003.1, U1001.B9 (CP1CA)
unnamed: C1003.2, U1001.B10 (CP1CB)
unnamed: C1004.1, U1001.A9 (CP1VOUTP)
unnamed: C1004.2, C1005.2
unnamed: C1005.1, U1001.A10 (CP1VOUTN)
unnamed: C1006.1, U1001.B11 (CP2CA)
unnamed: C1006.2, U1001.A11 (CP2CB)
unnamed: C1007.1, U1001.C11 (CP2VOUT)
unnamed: C1008.1, U1001.A5 (EPOUTN)
unnamed: C1009.1, U1001.A4 (EPOUTP)
unnamed: C1010.1, U1001.C13 (MICVDD)
unnamed: C1011.1, J1002.2, R1008.1, T1001.2 (-)
unnamed: C1011.2, C1012.2, C1013.2, C1014.2, T1001.1 (+), T1002.1 (+), T1003.1 (+), T1004.1 (+)
unnamed: C1012.1, J1002.1, R1007.1, T1002.2 (-)
unnamed: C1013.1, J1001.2, R1006.1, T1003.2 (-)
unnamed: C1014.1, J1001.1, R1005.1, T1004.2 (-)
unnamed: C1015.1, C1016.1, C1017.1
unnamed: C1015.2, C1016.2, C1017.2
unnamed: C1018.1, C1019.1, C1020.1, C1021.1, C1022.1, C1023.1, C1024.1, C1032.1, C1033.1
unnamed: C1018.2, C1019.2, C1020.2, C1021.2, C1022.2, C1023.2, C1024.2, C1032.2, C1033.2
unnamed: C1027.1, C1028.1
unnamed: C1027.2, C1028.2, C1029.2, C1030.2
unnamed: C1029.1, C1030.1
unnamed: C1031.1, U1003.6 (VCC)
unnamed: R1001.1, R1018.2
unnamed: R1001.2, U1001.F8 (SDA)
unnamed: R1002.1, R1019.2
unnamed: R1002.2, U1001.J11 (SCLK)
unnamed: R1003.2, U1001.H12 (MCLK1)
unnamed: R1004.2, U1001.F12 (MCLK2)
unnamed: R1005.2, U1001.F2 (SPKOUTLN)
unnamed: R1006.2, U1001.F1 (SPKOUTLP)
unnamed: R1007.2, U1001.J2 (SPKOUTRN)
unnamed: R1008.2, U1001.J1 (SPKOUTRP)
unnamed: R1013.1, U1001.J13 (SLIMCLK)
unnamed: R1014.1, U1001.G11 (SLIMDATA)
unnamed: R1015.1, U1001.J12 (AIF1BCLK)
unnamed: R1016.1, U1001.F10 (AIF1LRCLK)
unnamed: R1017.1, U1001.H11 (AIF1RXDAT)
unnamed: R1018.1, R1019.1
unnamed: TP1001.1, U1001.F13 (LDOENA)
unnamed: TP1002.1, U1001.D9 (~\\\\\RESET)
unnamed: TP1003.1, U1001.F11 (~\\\IRQ)
unnamed: U1001.A2 (AGND), U1001.B7 (AGND), U1001.C10 (CPGND), U1001.D5 (DGND), U1001.D6 (DGND), U1001.D7 (DGND), U1001.D8 (DGND), U1001.D10 (AGND), U1001.E4 (DGND), U1001.E5 (DGND), U1001.E6 (DGND), U1001.E7 (DGND), U1001.E8 (DGND), U1001.E9 (DGND), U1001.E10 (DGND), U1001.E12 (AGND), U1001.F4 (DGND), U1001.F6 (DGND), U1001.G1 (SPKGNDL), U1001.G2 (SPKGNDL), U1001.G6 (DGND), U1001.G13 (DGND), U1001.H1 (SPKGNDR), U1001.H2 (SPKGNDR), U1001.H4 (AGND), U1001.H6 (DGND)
unnamed: U1001.A3 (AVDD), U1001.A7 (AVDD), U1001.C9 (CPVDD), U1001.E13 (LDOVDD), U1001.G12 (DBVDD1), U1001.J4 (AVDD), U1001.J5 (DBVDD3), U1001.J7 (DBVDD2), U1001.J10 (DBVDD1)
unnamed: U1001.E1 (SPKVDDL), U1001.E2 (SPKVDDL), U1001.E3 (SPKVDDL), U1001.F3 (SPKVDDL), U1001.G3 (SPKVDDL), U1001.H3 (SPKVDDR), U1001.J3 (SPKVDDR)
unnamed: U1002.5 (G2), U1003.4 (Y)
WM8998_GPIO5: TP1004.1, U1001.E11 (GPIO5), U1002.2 (G1), U1003.2 (A)

Notes on the sheet:
DCVDD 1.2V DCVDD 1.8V DVDD1 1.8V DBVDD2 DBVDD3 1.7V ---------3.47V LDOVDD 1.8V CPVDD 1.8V SPKVDDL SPKVDDR 2.4V-----5.5V AVDD 1.8V
Audio Codec
PDNM6N30V7
