state-of-the-art/binocular/design/prototype_1/kicad/prototype_testboard-1/11_SENSOR.kicad_sch

## KiCad design design/prototype_1/kicad/prototype_testboard-1/11_SENSOR.kicad_sch (2022-01-14)

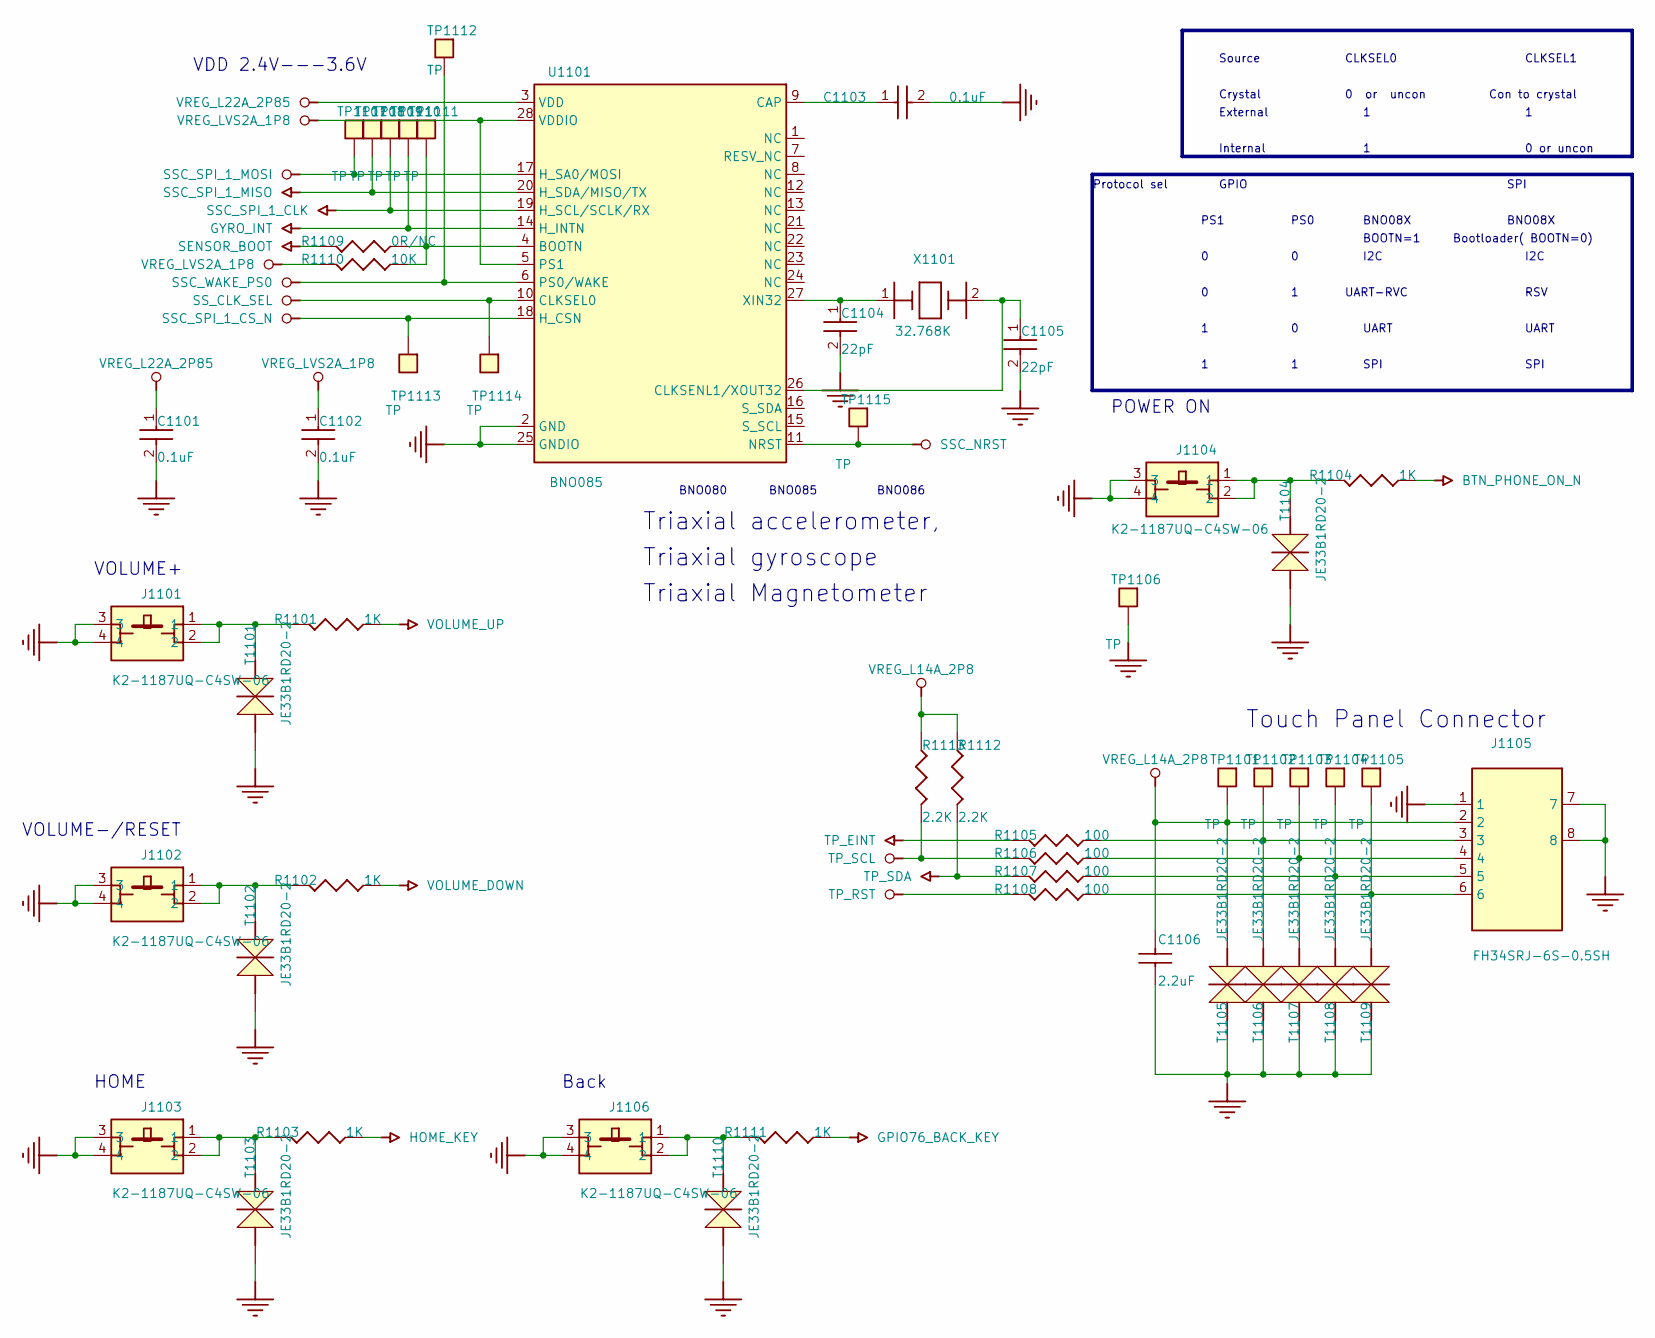
[picture p33: schematic 11_SENSOR.kicad_sch]

Parts:
C1101, C1102, C1103: 0.1uF; C0201
C1104, C1105: 22pF; C0201
C1106: 2.2uF; C0402
J1101, J1102, J1103, J1104, J1106: K2-1187UQ-C4SW-06; K2-1187UQ
J1105: FH34SRJ-6S-0.5SH; IO8-P0.5-5X3-T1.0
R1101, R1102, R1103, R1104, R1111: 1K; R0201
R1105, R1106, R1107, R1108: 100; R0201
R1109: 0R/NC; R0201
R1110: 10K; R0201
R1112, R1113: 2.2K; R0201
T1101, T1102, T1106, T1107, T1108: JE33B1RD20-2; DFN1006-2; PART NUMBER TY01100606
T1103, T1104, T1105, T1109, T1110: JE33B1RD20-2; DFN1006-2; MANUFACTURER PART NUMBER RB551V-30TE-17
TP1101, TP1102, TP1103, TP1104, TP1105, TP1106, TP1107, TP1108, TP1109, TP1110, TP1111, TP1112, TP1113, TP1114, TP1115: TP; TP-D1r0
U1101: BNO085; BNO08X_LGA_28P
X1101: 32.768K; CRY2012

Connections:
unnamed: C1103.1, U1101.9 (CAP)
unnamed: C1104.1, U1101.27 (XIN32), X1101.1
unnamed: C1105.1, U1101.26 (CLKSENL1/XOUT32), X1101.2
unnamed: C1106.1, T1105.1 (+), T1106.1 (+), T1107.1 (+), T1108.1 (+), T1109.1 (+)
unnamed: C1106.2, J1105.2, T1105.2 (-), TP1101.1
unnamed: J1101.1, J1101.2, R1101.2, T1101.2 (-)
unnamed: J1101.3, J1101.4
unnamed: J1102.1, J1102.2, R1102.2, T1102.2 (-)
unnamed: J1102.3, J1102.4
unnamed: J1103.1, J1103.2, R1103.2, T1103.2 (-)
unnamed: J1103.3, J1103.4
unnamed: J1104.1, J1104.2, R1104.2, T1104.2 (-)
unnamed: J1104.3, J1104.4
unnamed: J1105.3, R1105.1, T1106.2 (-), TP1102.1
unnamed: J1105.4, R1106.1, T1107.2 (-), TP1103.1
unnamed: J1105.5, R1107.1, T1108.2 (-), TP1104.1
unnamed: J1105.6, R1108.1, T1109.2 (-), TP1105.1
unnamed: J1105.7, J1105.8
unnamed: J1106.1, J1106.2, R1111.2, T1110.2 (-)
unnamed: J1106.3, J1106.4
unnamed: R1106.2, R1113.2
unnamed: R1107.2, R1112.2
unnamed: R1109.1, R1110.1, TP1111.1, U1101.4 (BOOTN)
unnamed: R1112.1, R1113.1
unnamed: TP1107.1, U1101.17 (H_SA0/MOSI)
unnamed: TP1108.1, U1101.20 (H_SDA/MISO/TX)
unnamed: TP1109.1, U1101.19 (H_SCL/SCLK/RX)
unnamed: TP1110.1, U1101.14 (H_INTN)
unnamed: TP1112.1, U1101.6 (PS0/WAKE)
unnamed: TP1113.1, U1101.18 (H_CSN)
unnamed: TP1114.1, U1101.10 (CLKSEL0)
unnamed: TP1115.1, U1101.11 (NRST)
unnamed: U1101.2 (GND), U1101.25 (GNDIO)
unnamed: U1101.5 (PS1), U1101.28 (VDDIO)

Notes on the sheet:
CLKSEL0
External
Source
PS0
Triaxial accelerometer,
BNO080
RSV
Back
HOME
SPI
I2C
0 or uncon
CLKSEL1
0 or uncon
PS1
Triaxial gyroscope
VDD 2.4V---3.6V
UART
BNO08X
Bootloader( BOOTN=0)
VOLUME-/RESET
Crystal
BNO086
Internal
VOLUME+
Con to crystal
BNO085
POWER ON
Touch Panel Connector
BOOTN=1
Protocol sel
GPIO
Triaxial Magnetometer
UART-RVC
